kumarobo/PlaRails/Crossover/RailVCoverCV_pointtestasm.png

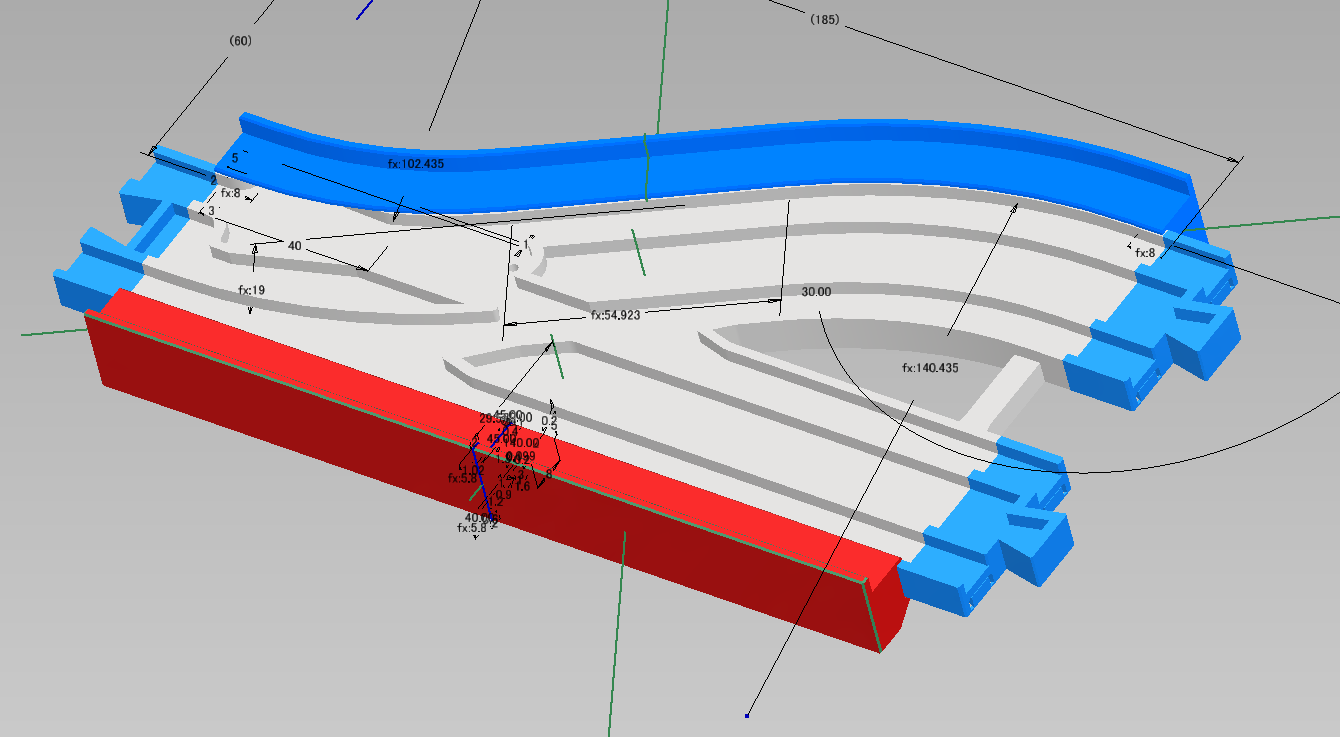
Crossover/RailVCoverCV_pointtestasm.png
