kumarobo/PlaRails/Crossover/RailVCoverCV_S.png

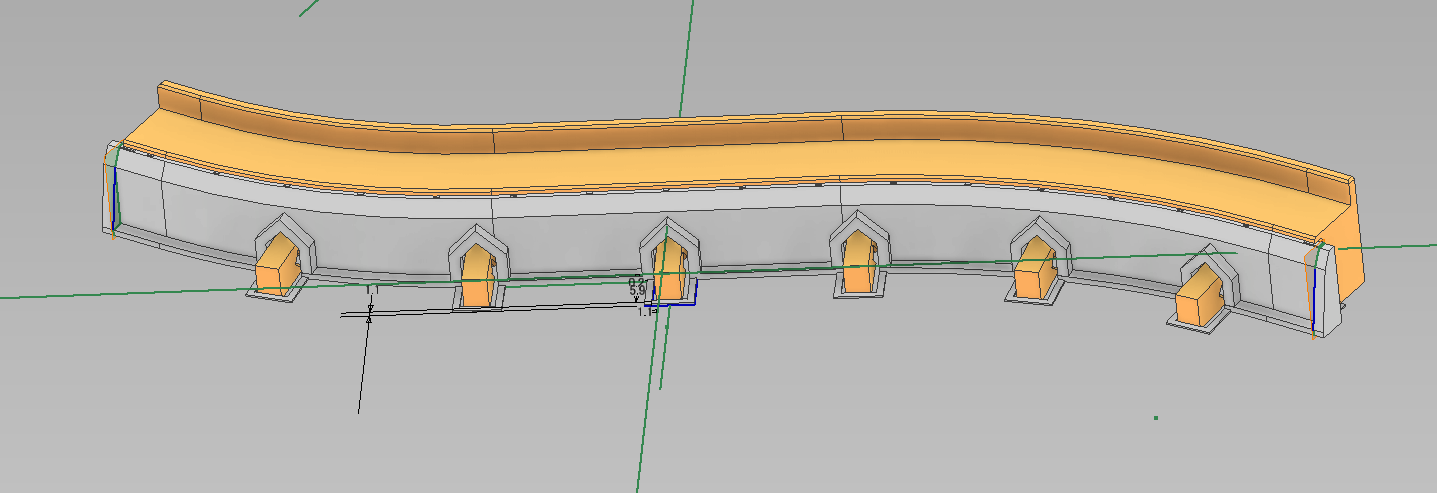
Crossover/RailVCoverCV_S.png
