kumarobo/PlaRails/Crossover/RailVCoverST.png

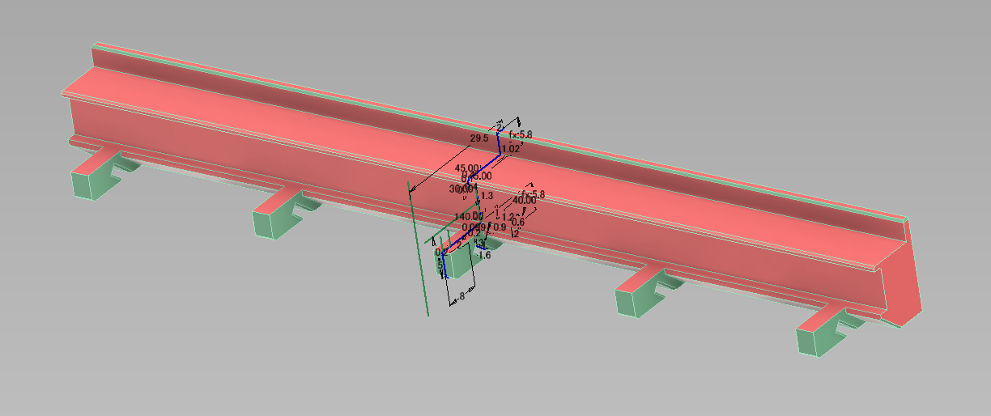
Crossover/RailVCoverST.png
