kumarobo/PlaRails/Crossover/SingleCross.png

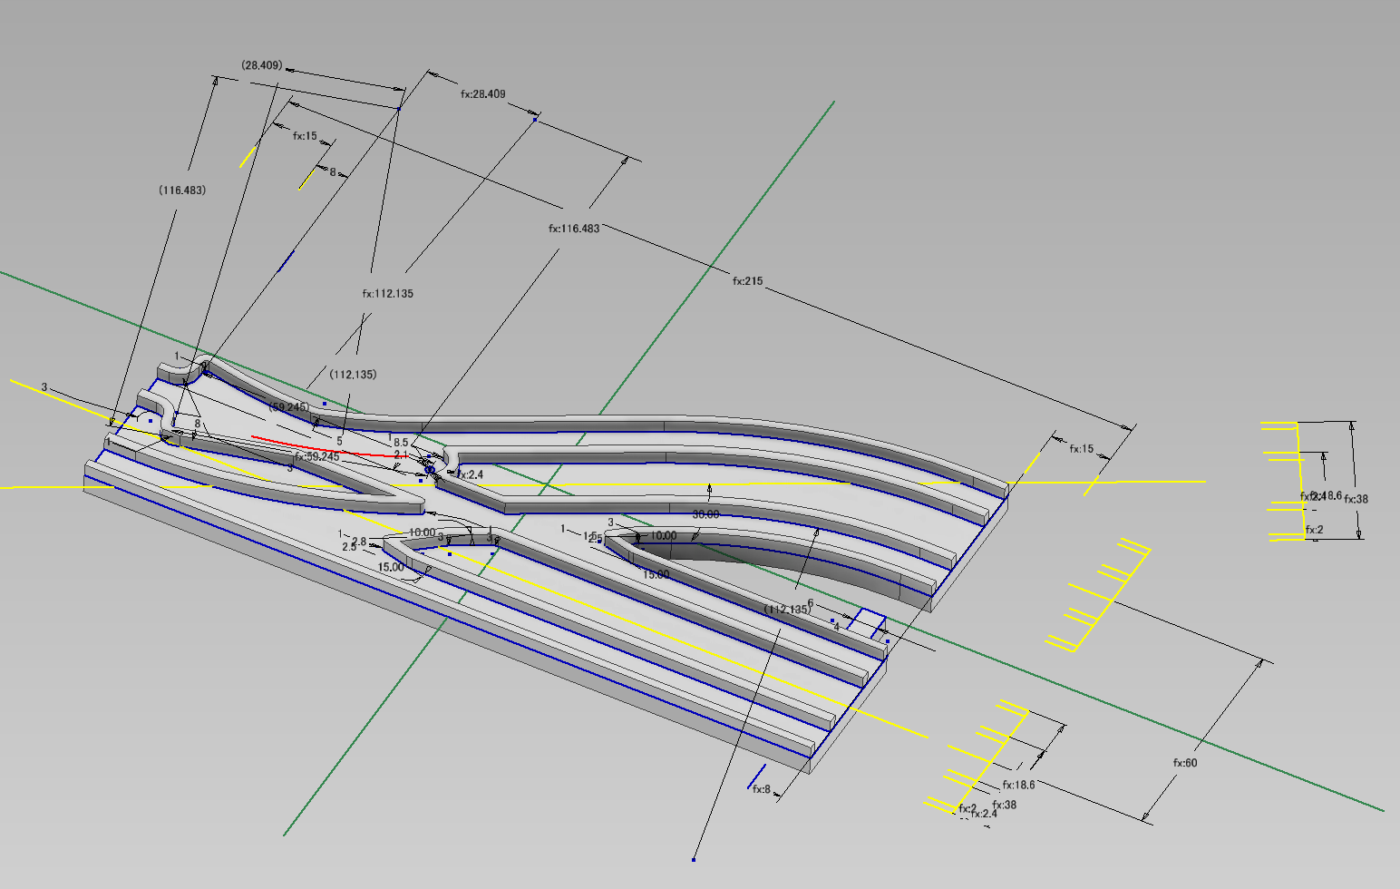
Crossover/SingleCross.png
