kumarobo/PlaRails/Crossover/SingleCrossoverIA.png

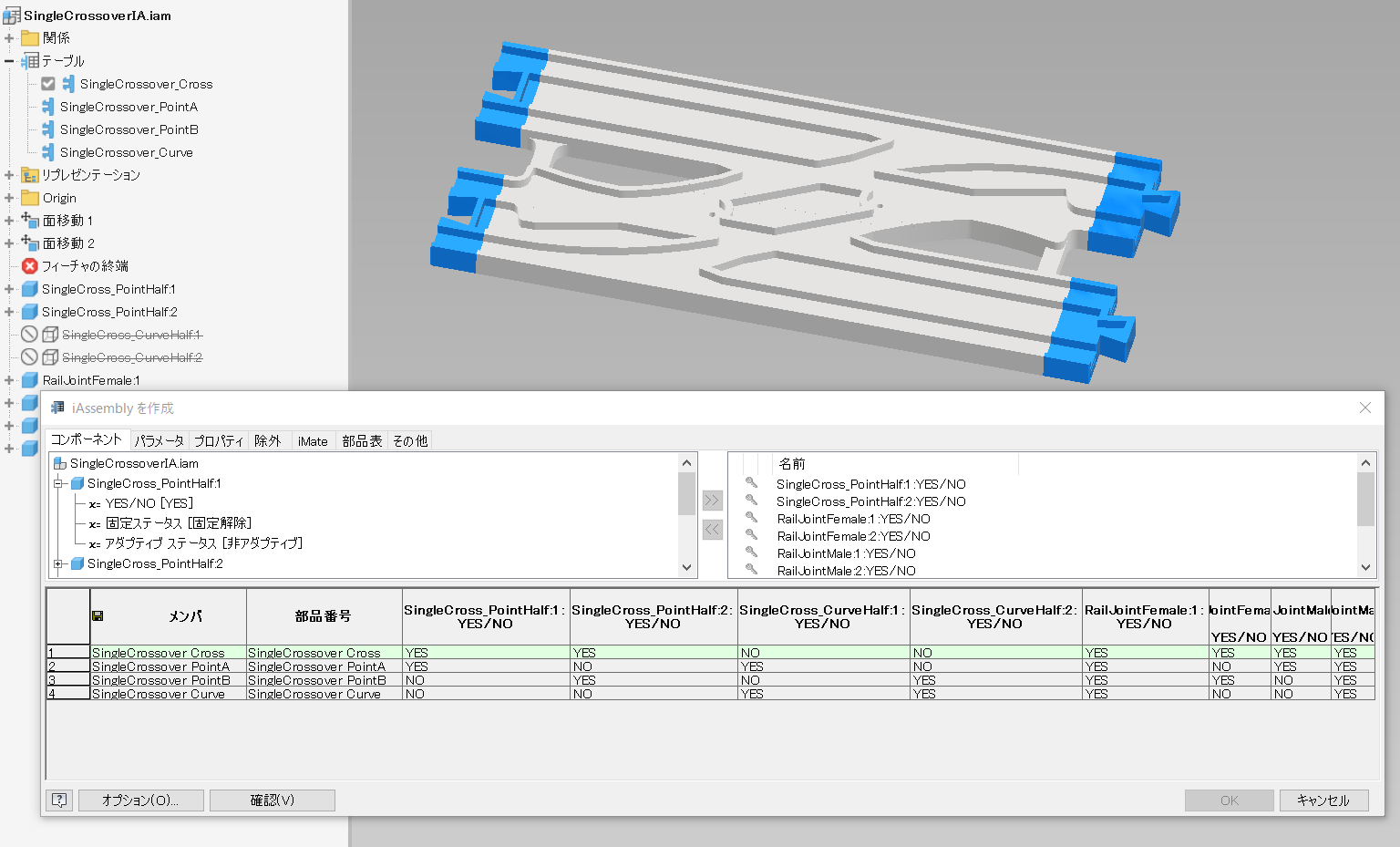
Crossover/SingleCrossoverIA.png
