kumarobo/PlaRails/Crossover/SingleCrossoverIA_Cross.png

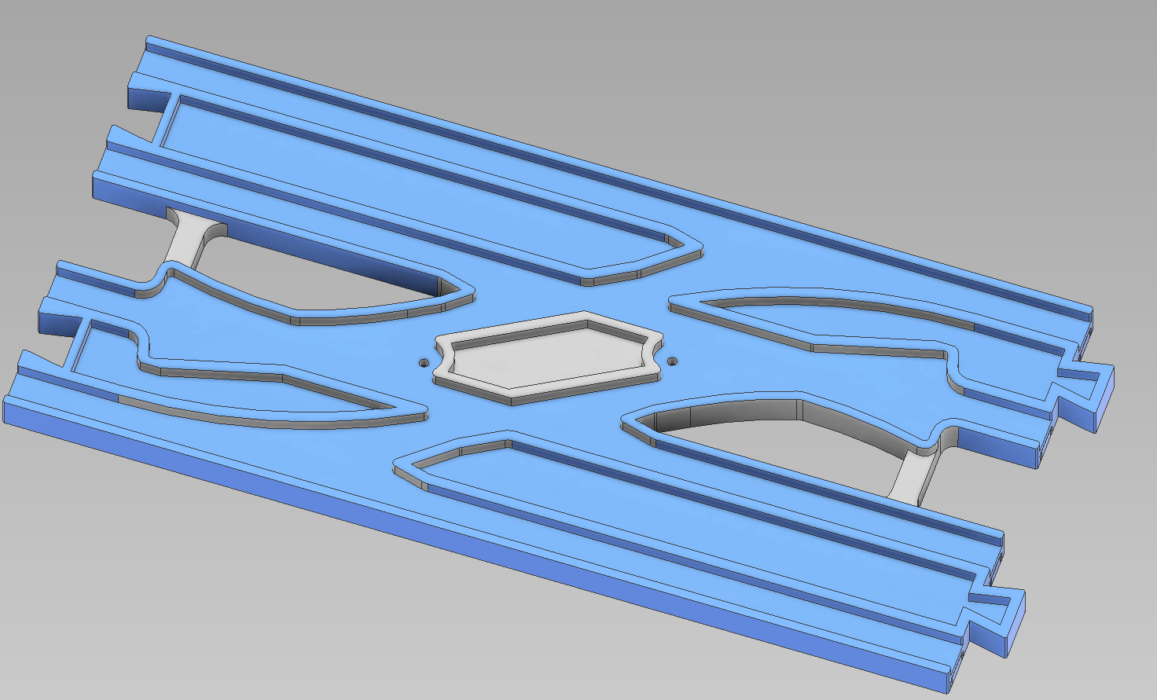
Crossover/SingleCrossoverIA_Cross.png
