kumarobo/PlaRails/Crossover/SingleCrossoverIA_Cross_MIR.png

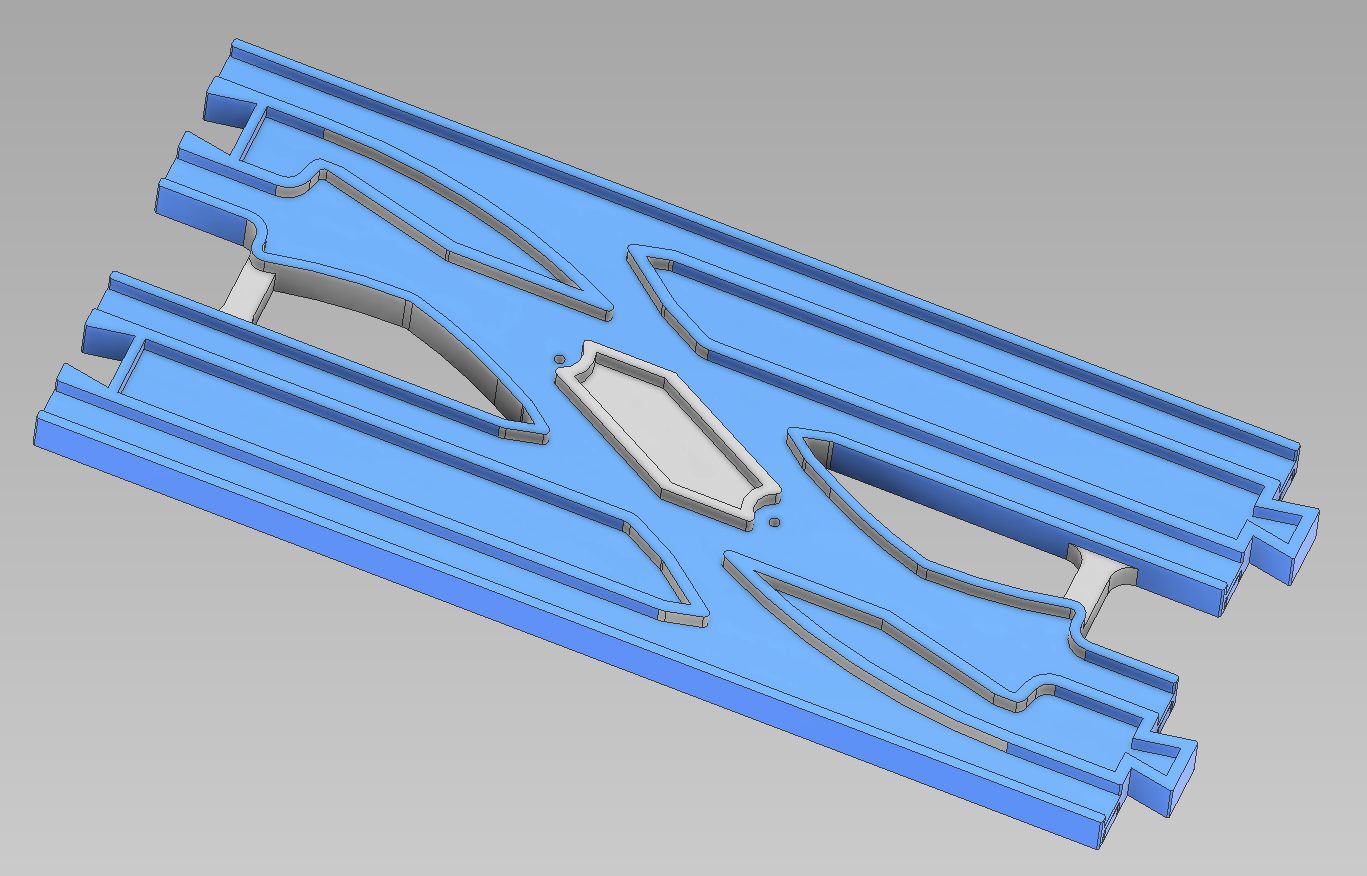
Crossover/SingleCrossoverIA_Cross_MIR.png
