kumarobo/PlaRails/Crossover/SingleCrossoverIA_Curve.png

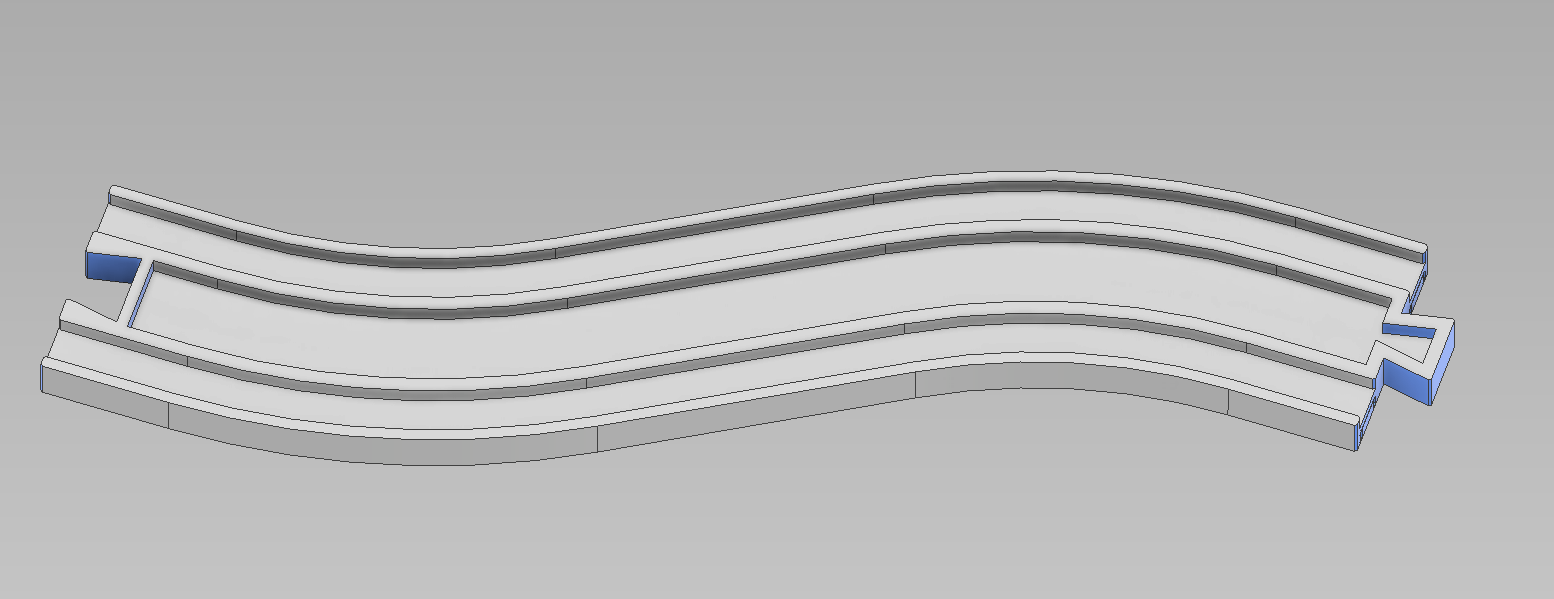
Crossover/SingleCrossoverIA_Curve.png
