kumarobo/PlaRails/Crossover/SingleCrossoverIA_Curve_MIR.png

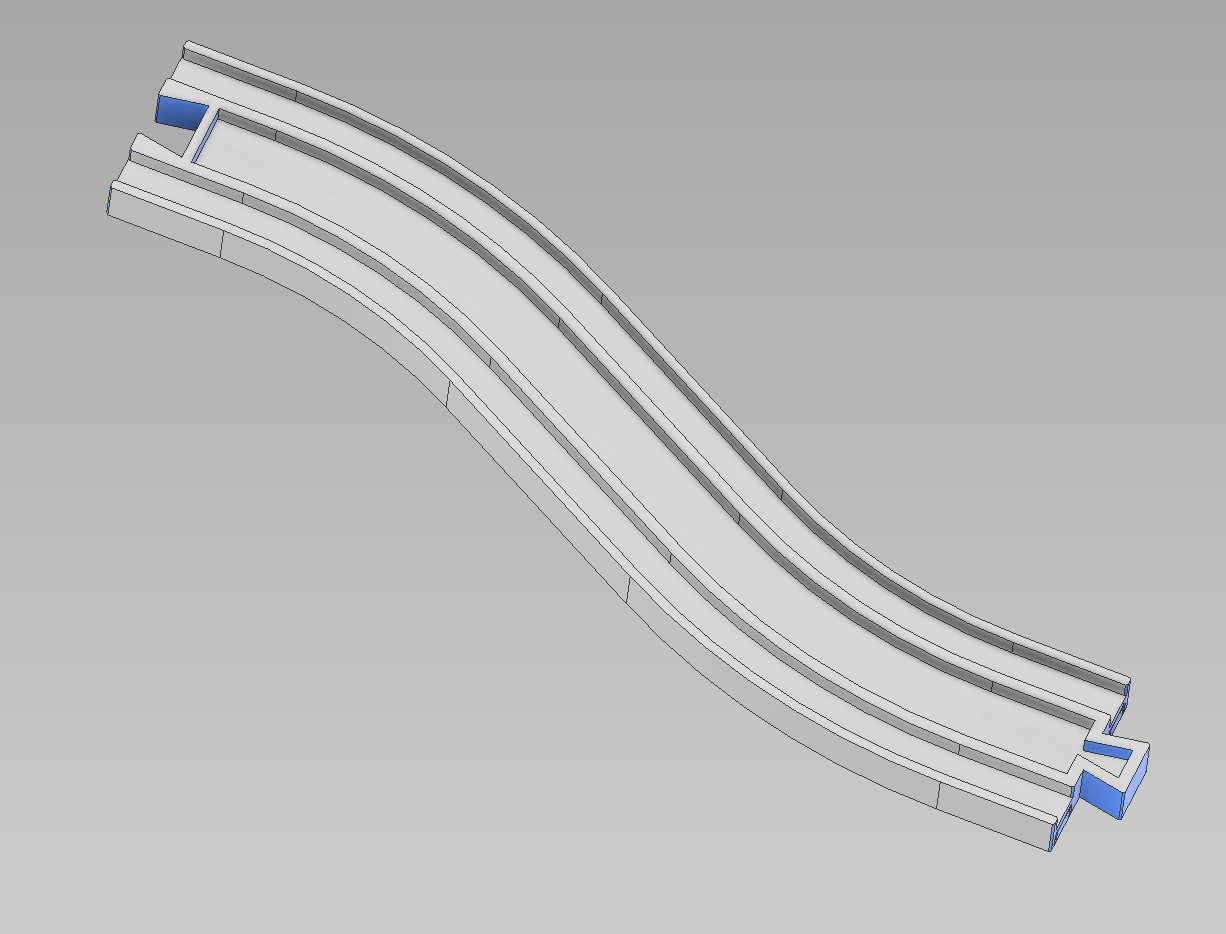
Crossover/SingleCrossoverIA_Curve_MIR.png
