kumarobo/PlaRails/Crossover/SingleCrossoverIA_PointA.png

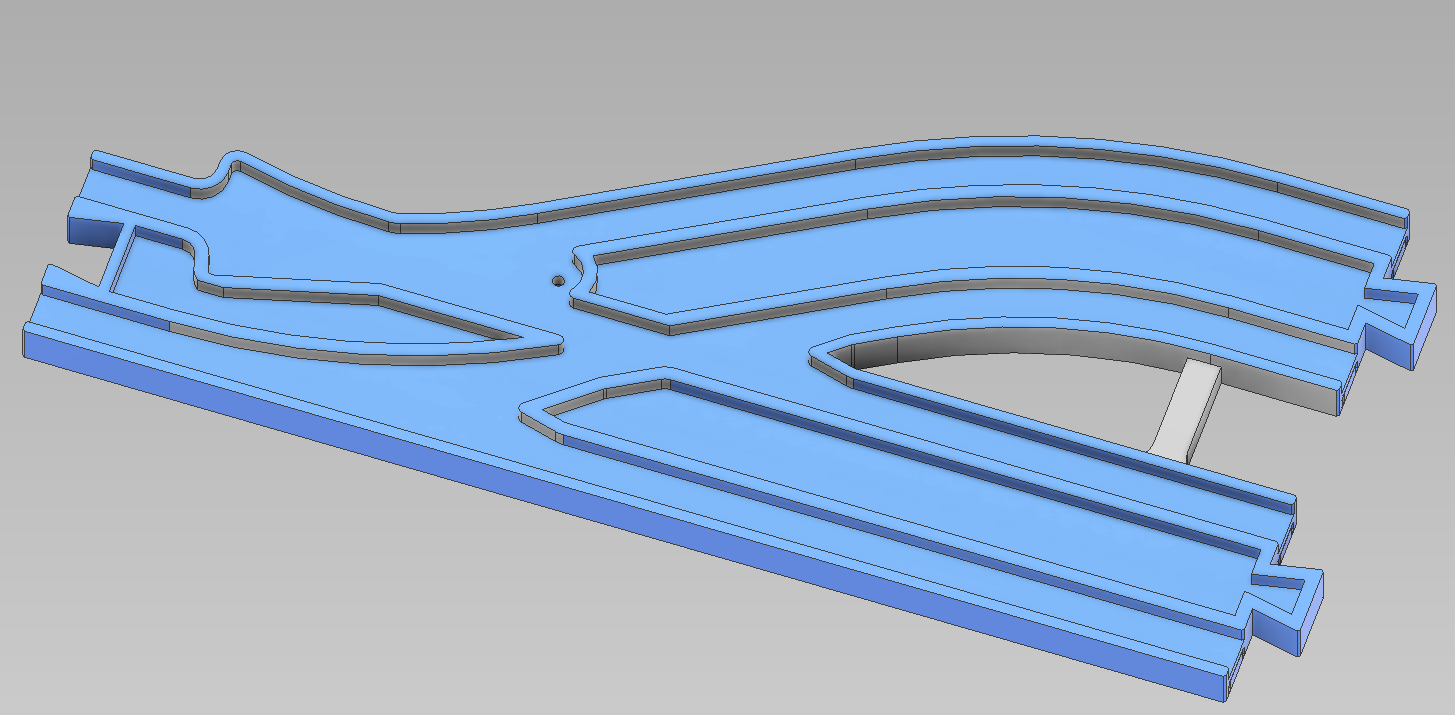
Crossover/SingleCrossoverIA_PointA.png
