kumarobo/PlaRails/Crossover/SingleCrossoverIA_PointA_MIR.png

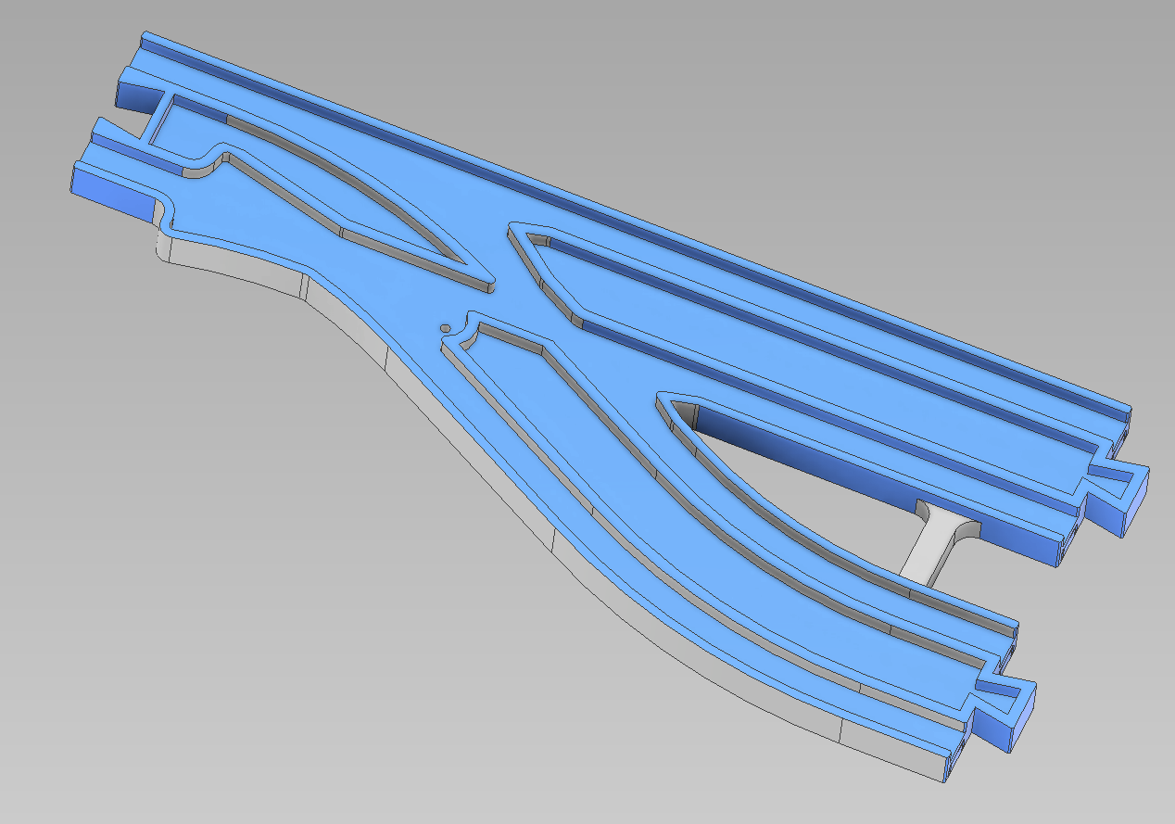
Crossover/SingleCrossoverIA_PointA_MIR.png
