kumarobo/PlaRails/CurveRail/CurveRail-89-25.png

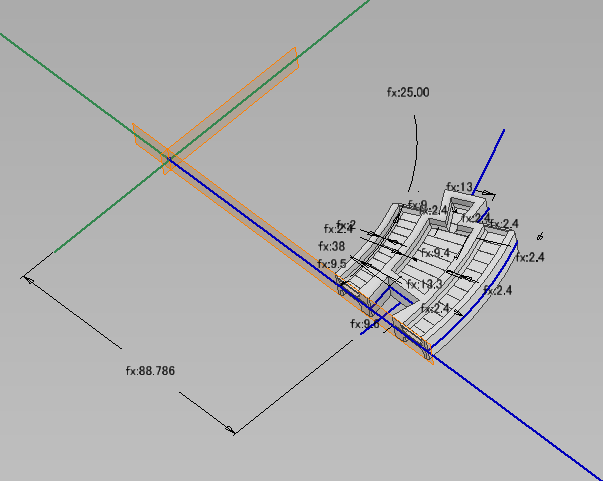
CurveRail/CurveRail-89-25.png
