kumarobo/PlaRails/CurveRail/CurveRail-215-45.png

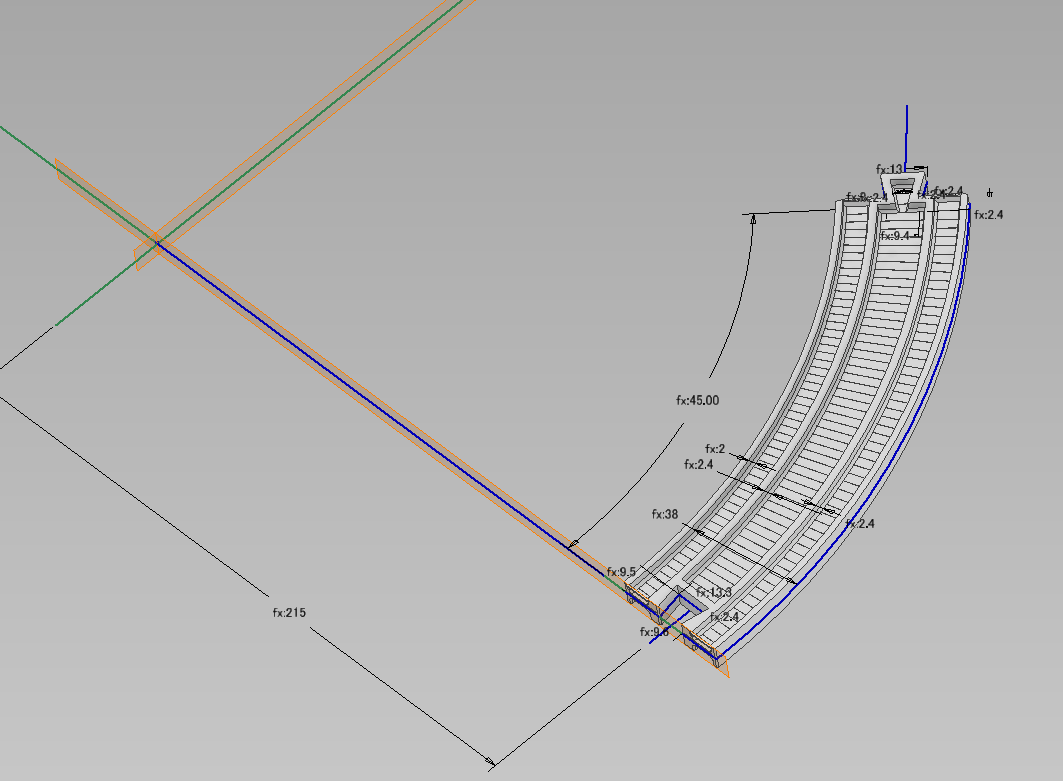
CurveRail/CurveRail-215-45.png
