kumarobo/PlaRails/CurveRail/CurveRail-215half-45.png

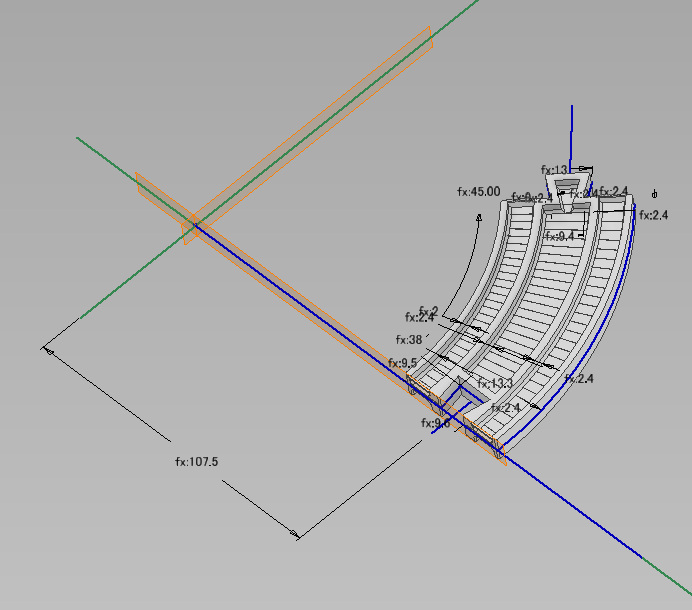
CurveRail/CurveRail-215half-45.png
