kumarobo/PlaRails/CurveRail/CurveRail-215half-90.png

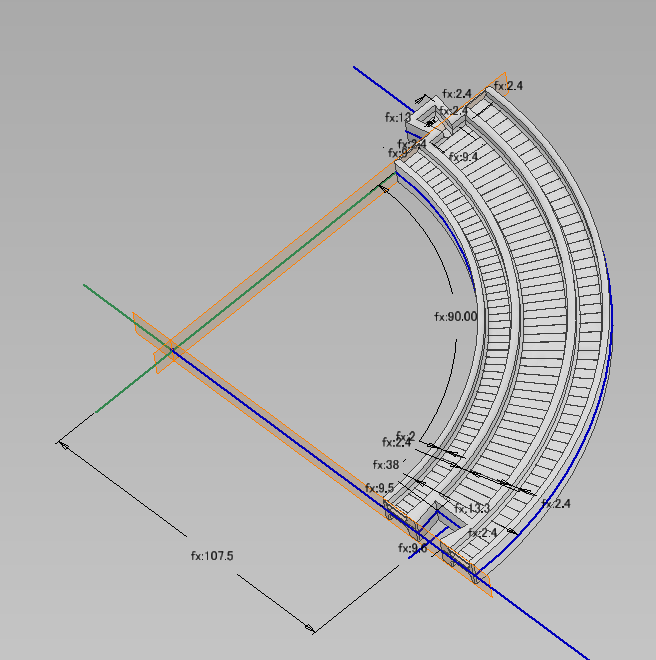
CurveRail/CurveRail-215half-90.png
