kumarobo/PlaRails/CurveRail/CurveRail-342-25.png

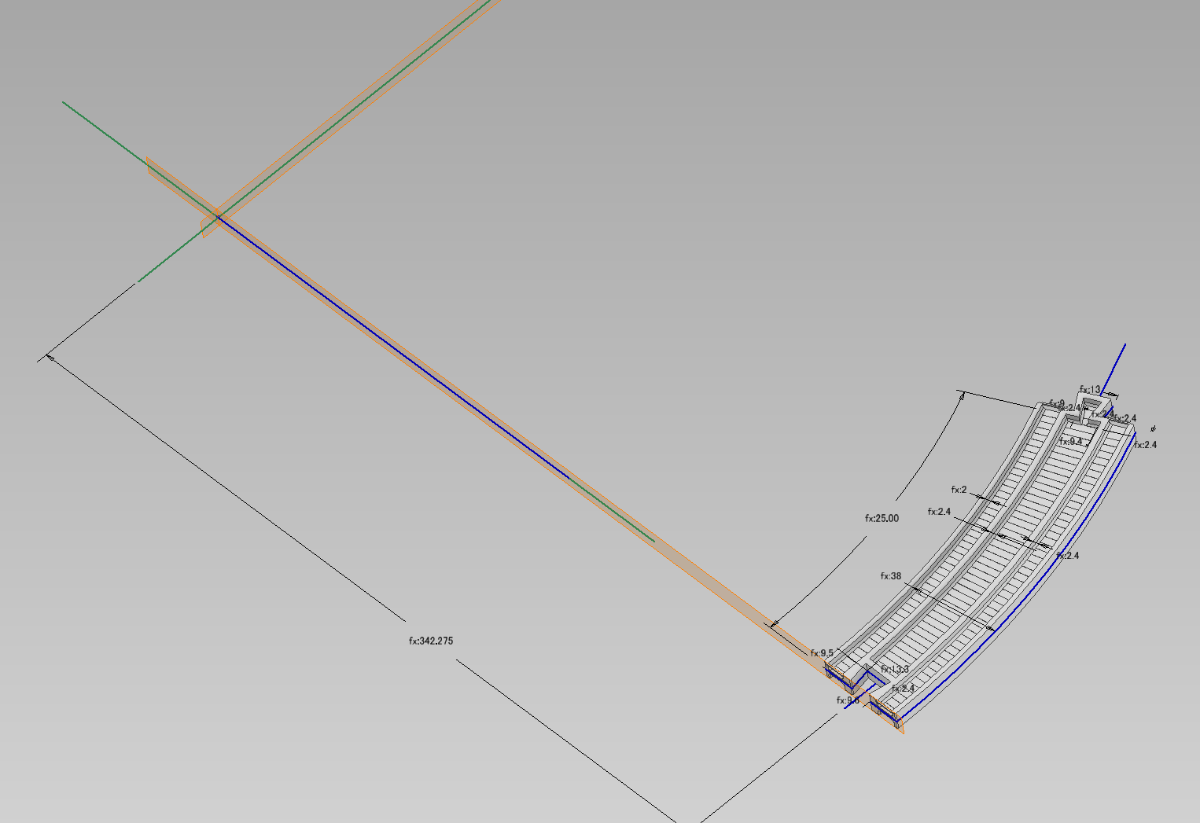
CurveRail/CurveRail-342-25.png
