kumarobo/PlaRails/DoubleCross/DoubleCross.png

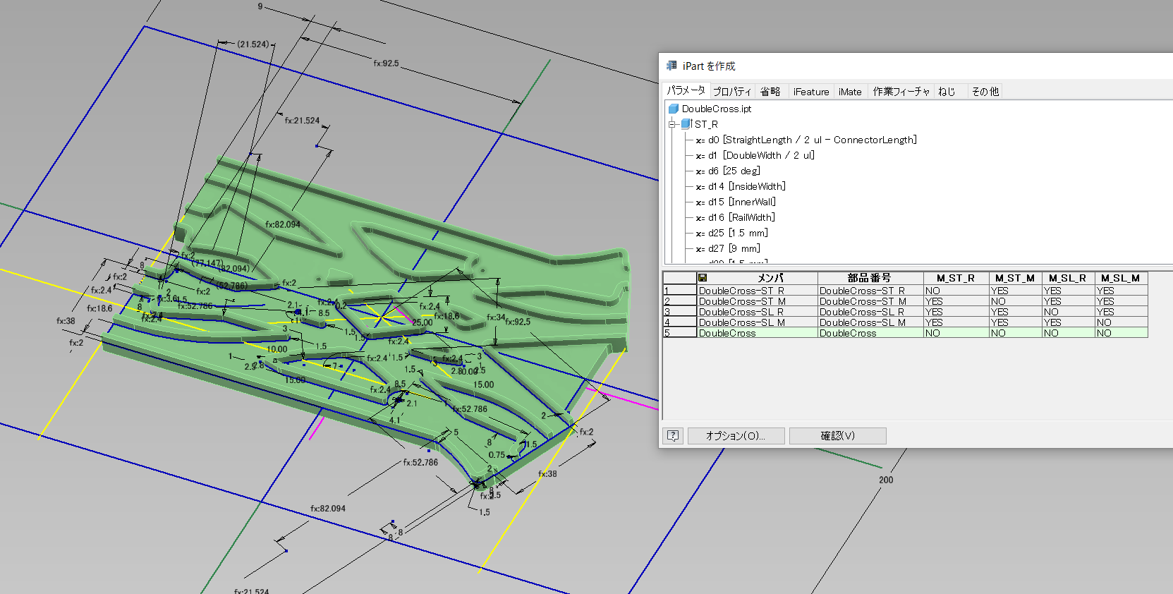
DoubleCross/DoubleCross.png
