kumarobo/PlaRails/DoubleCross/DoubleCross_DoubleSlant.png

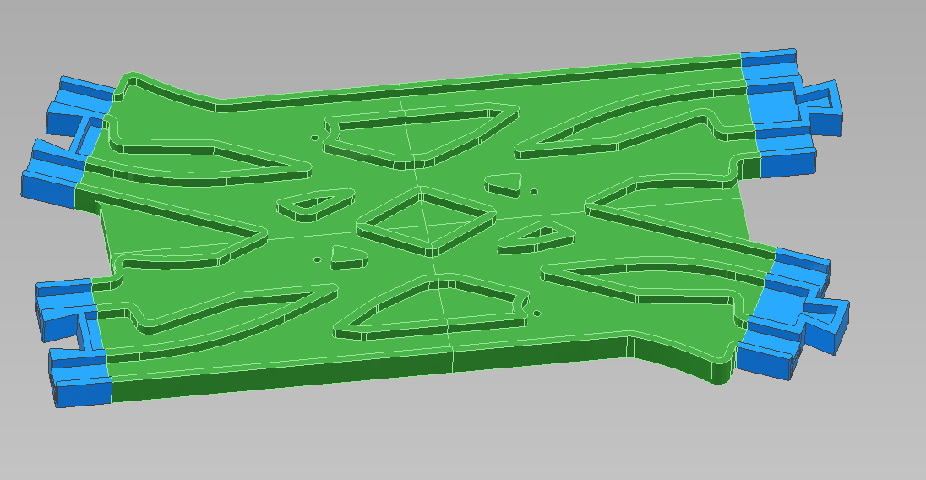
DoubleCross/DoubleCross_DoubleSlant.png
