kumarobo/PlaRails/DoubleCross/DoubleCross_DoubleSlip_C.png

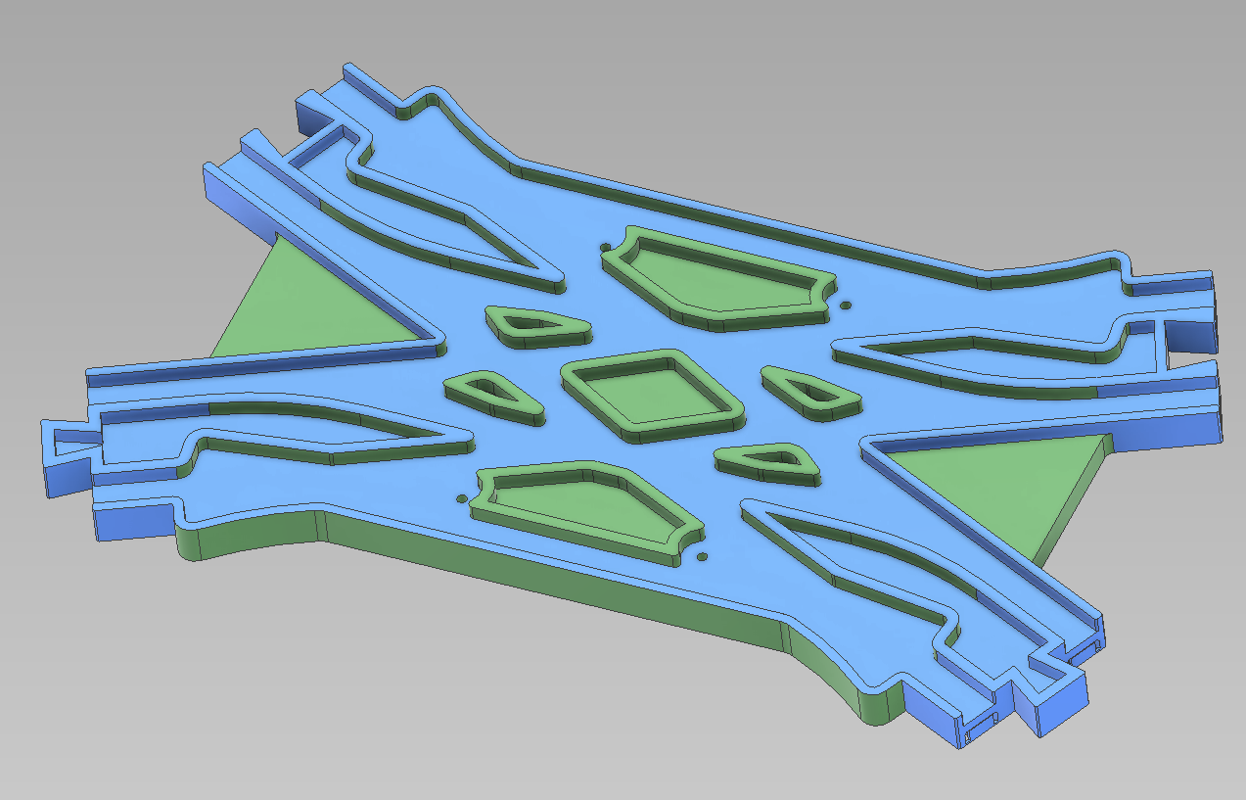
DoubleCross/DoubleCross_DoubleSlip_C.png
