kumarobo/PlaRails/DoubleCross/DoubleCross_Rturn_C.png

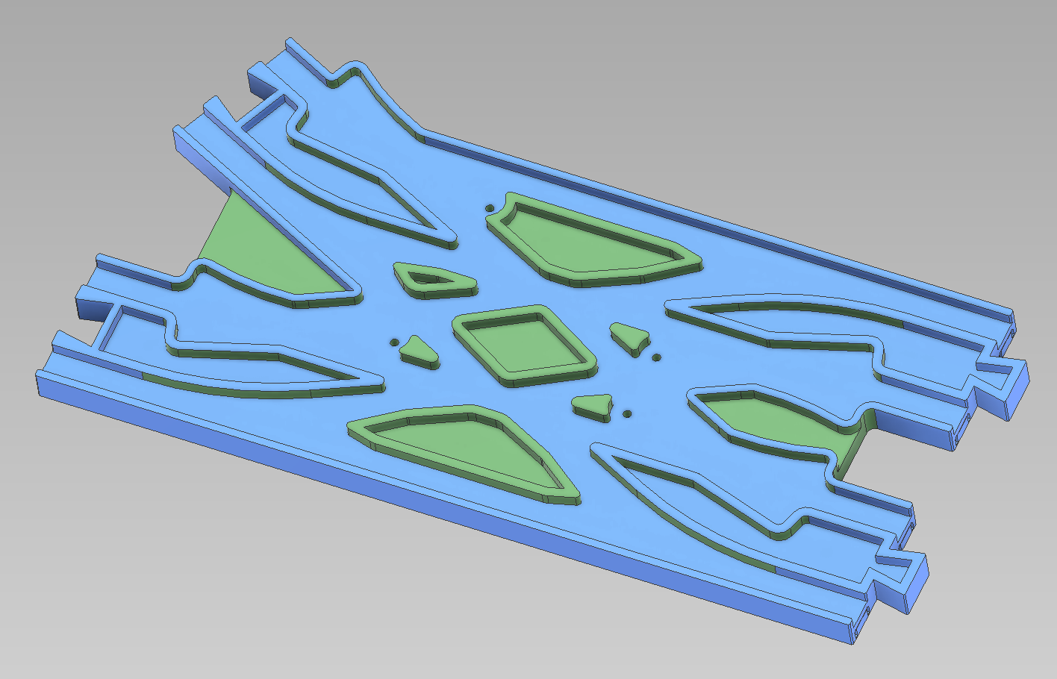
DoubleCross/DoubleCross_Rturn_C.png
