kumarobo/PlaRails/DoubleCross/DoubleCross_Straight_C.png

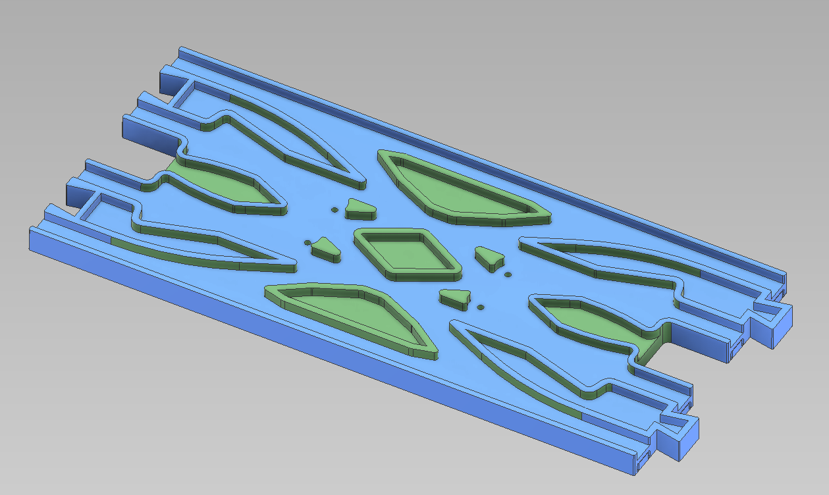
DoubleCross/DoubleCross_Straight_C.png
