kumarobo/PlaRails/DoubleCross/DoubleCross_SymWiden_C.png

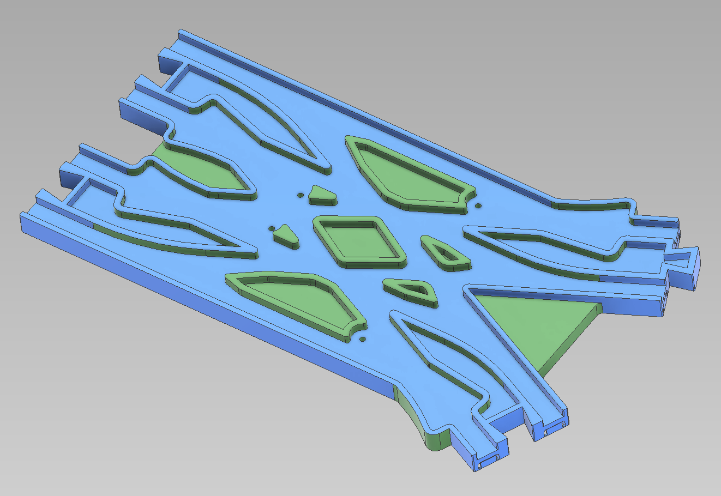
DoubleCross/DoubleCross_SymWiden_C.png
