kumarobo/PlaRails/DoubleSlip/CrossRail_C_DSS.png

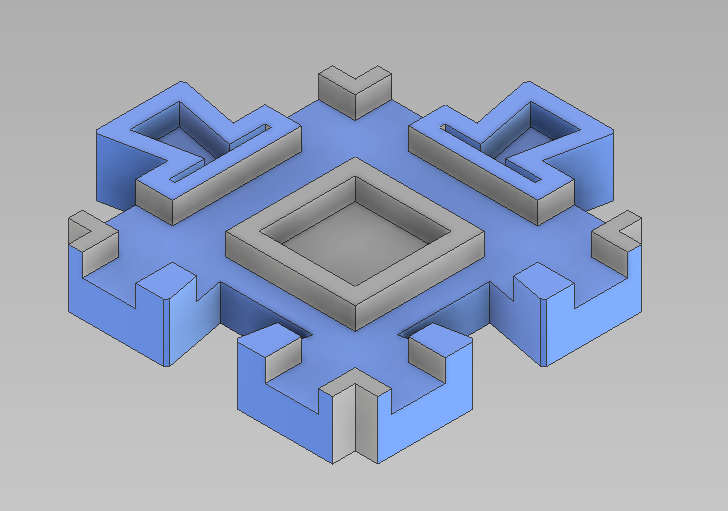
DoubleSlip/CrossRail_C_DSS.png
