kumarobo/PlaRails/DoubleSlip/DoubleSlipHR_asmtest.png

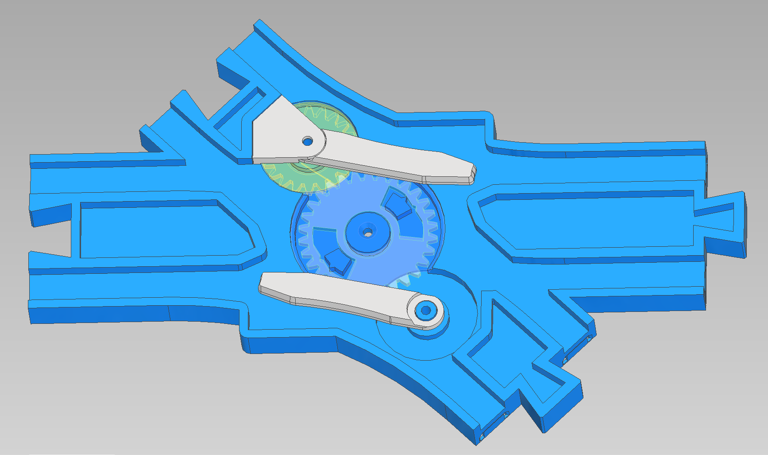
DoubleSlip/DoubleSlipHR_asmtest.png
