kumarobo/PlaRails/DoubleSlip/DoubleSlipHR_C_H_H.png

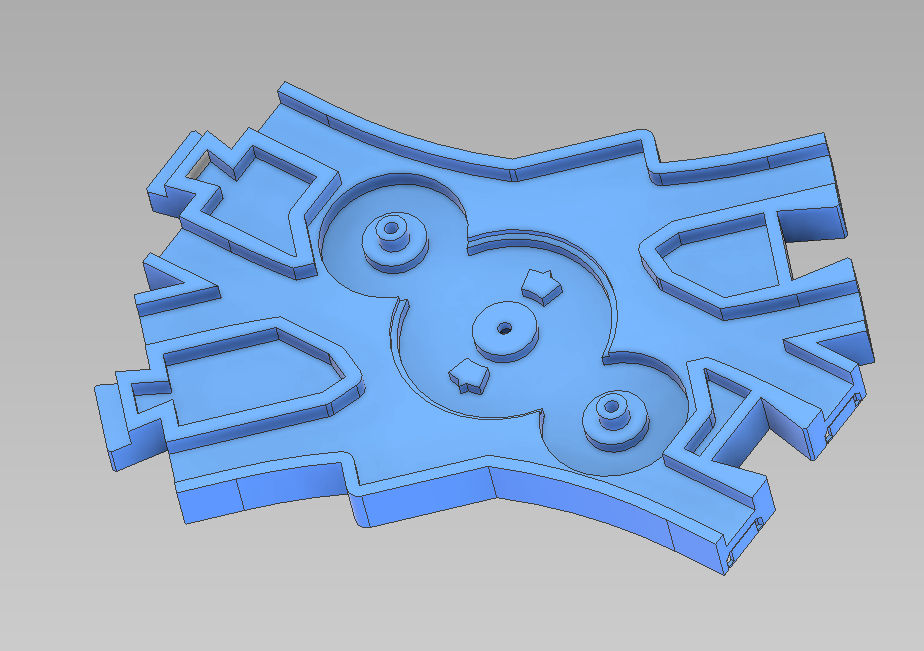
DoubleSlip/DoubleSlipHR_C_H_H.png
