kumarobo/PlaRails/DoubleSlip/DoubleSlipHR_C_H_HS.png

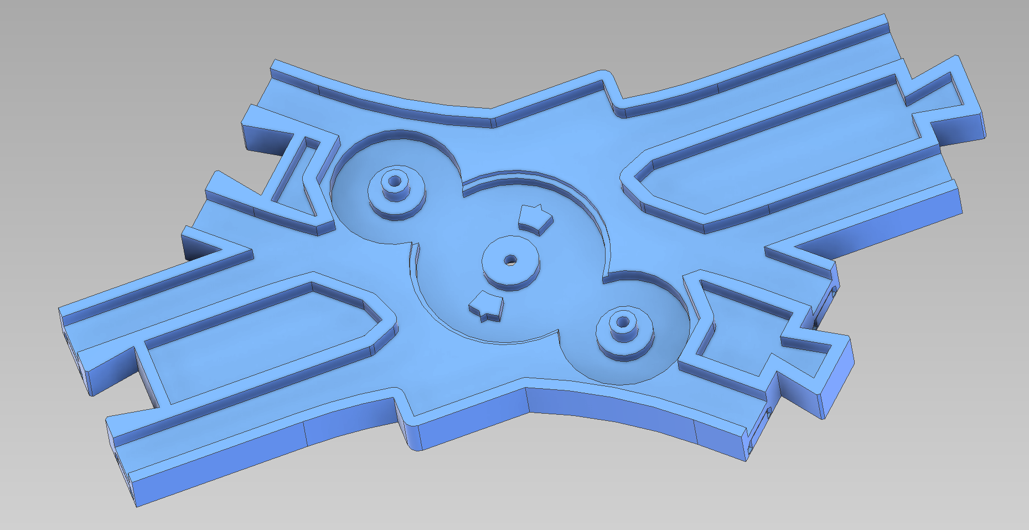
DoubleSlip/DoubleSlipHR_C_H_HS.png
