kumarobo/PlaRails/DoubleSlip/DoubleSlipHR_C_HS_H.png

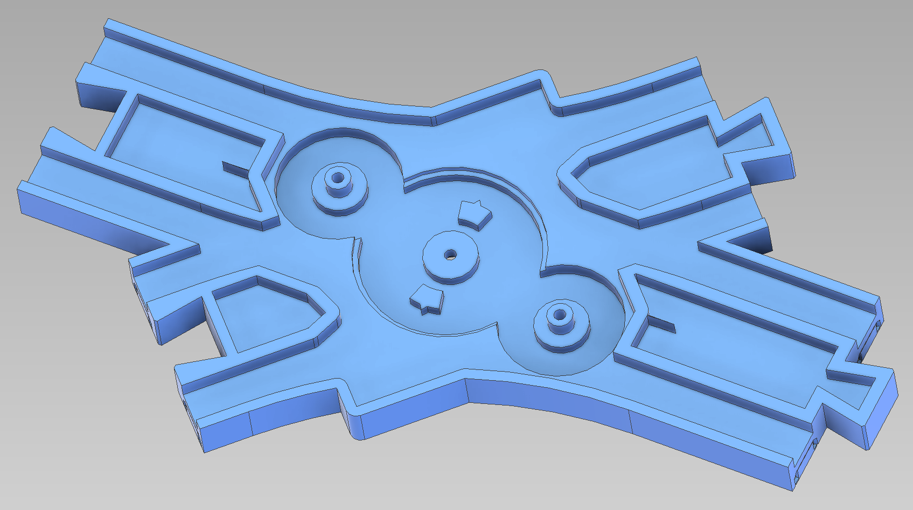
DoubleSlip/DoubleSlipHR_C_HS_H.png
