kumarobo/PlaRails/Misc/AsterMale_6.png

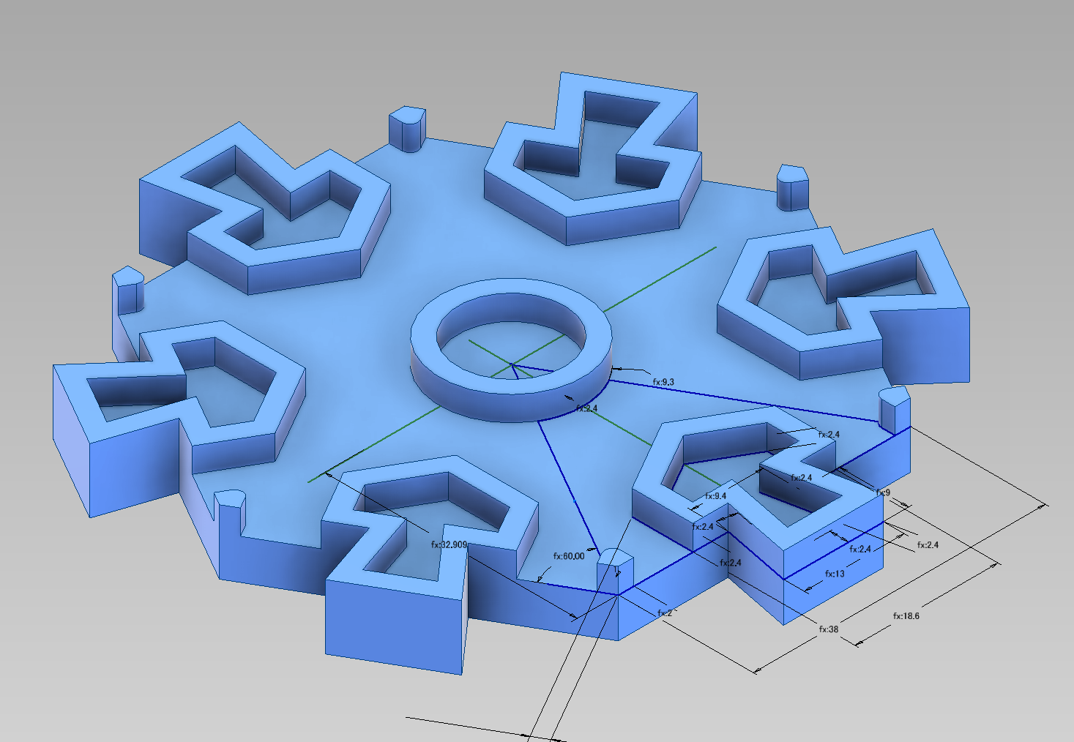
Misc/AsterMale_6.png
