kumarobo/PlaRails/PocketTrackPoint/PocketPoint.png

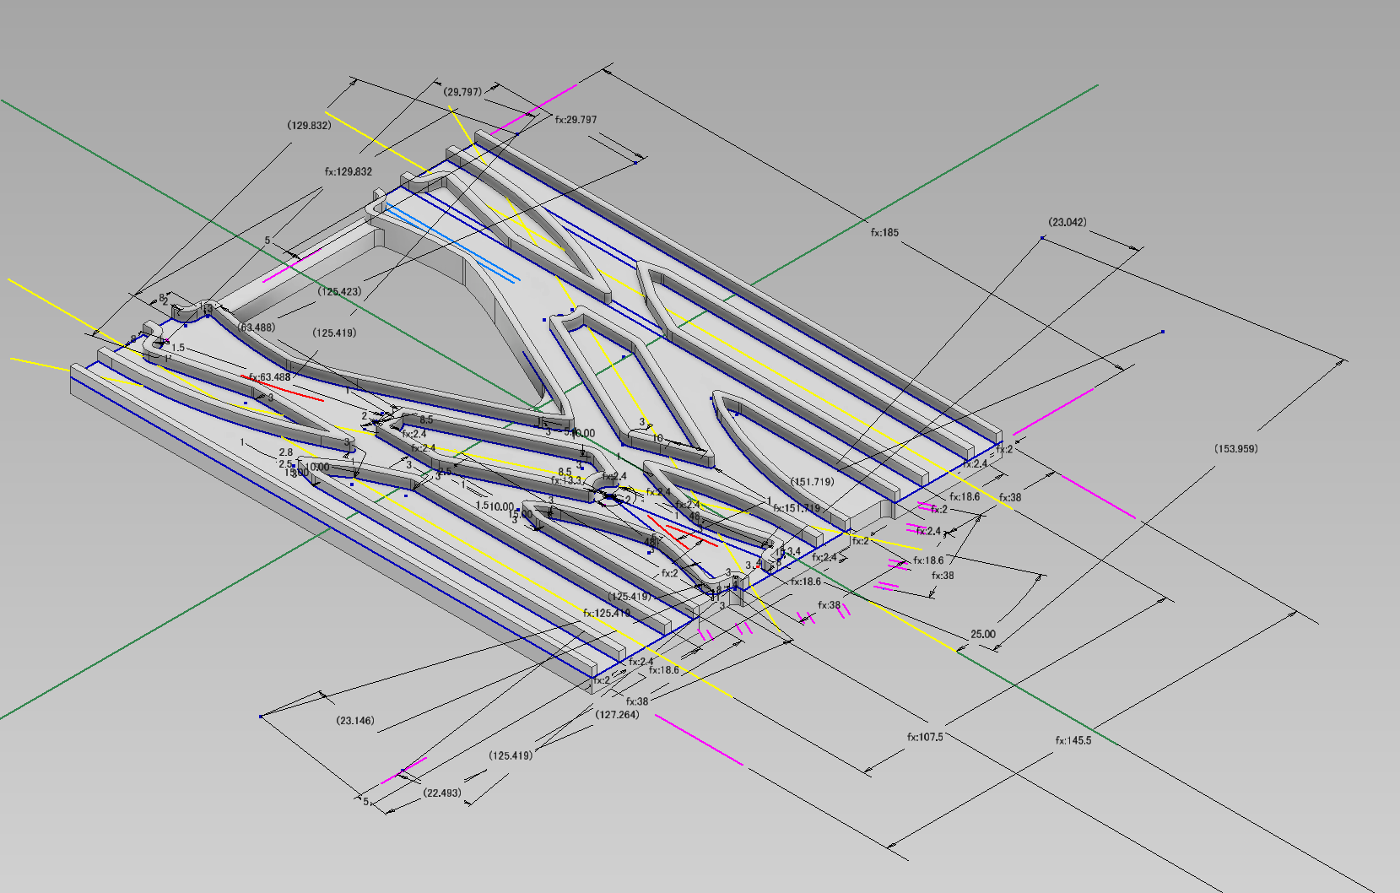
PocketTrackPoint/PocketPoint.png
