kumarobo/PlaRails/PocketTrackPoint/PocketPoint_C.png

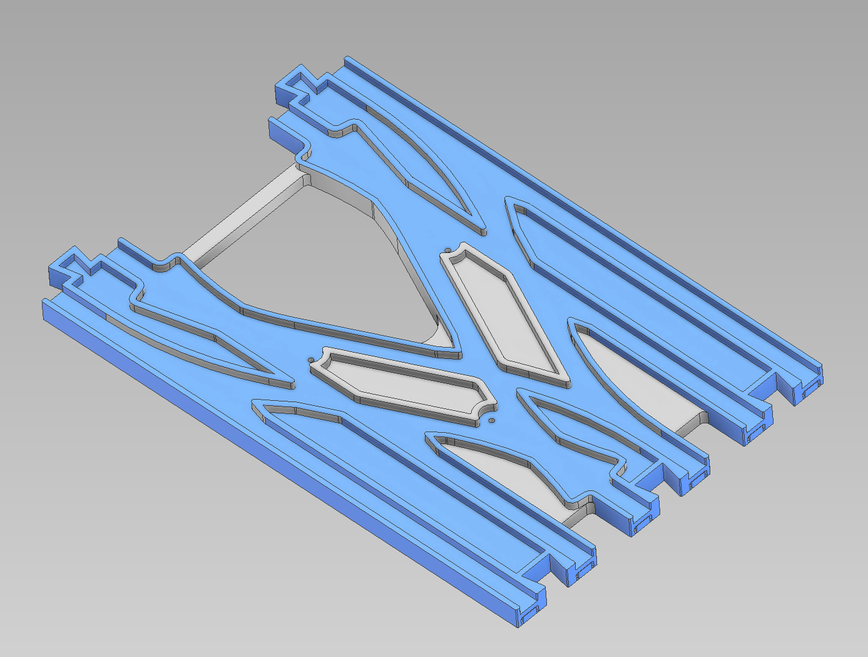
PocketTrackPoint/PocketPoint_C.png
