kumarobo/PlaRails/ShiftRail/ShiftRail_C.png

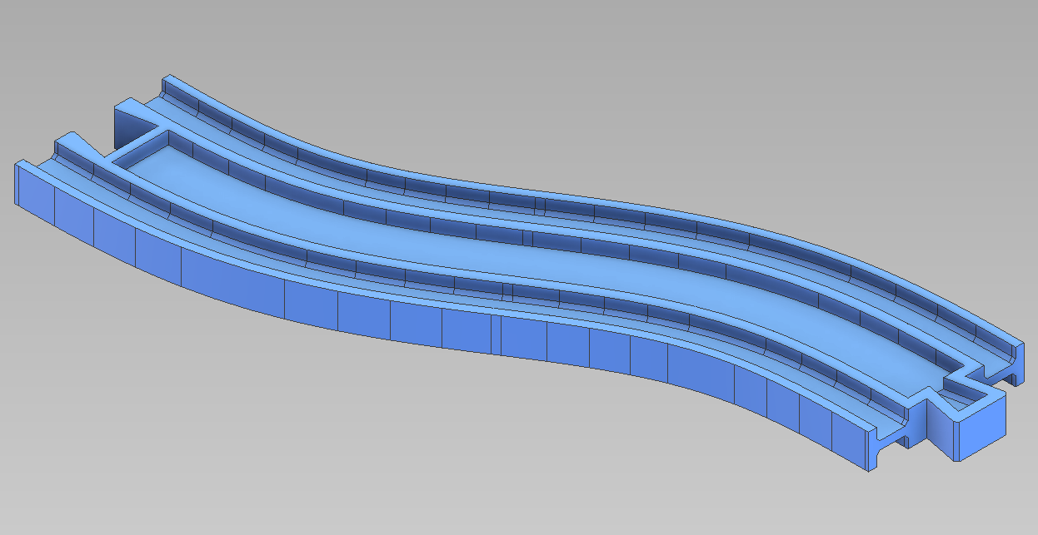
ShiftRail/ShiftRail_C.png
