kumarobo/PlaRails/ShiftRail/ShiftRail_ipt.png

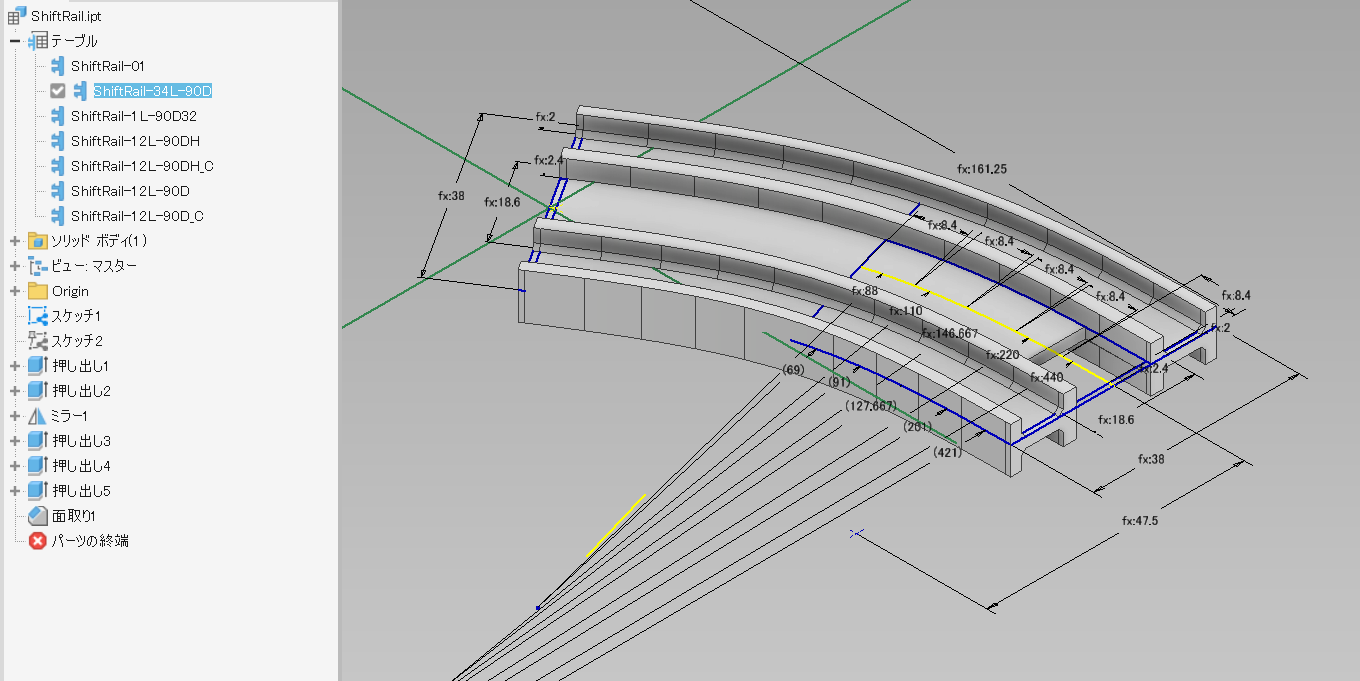
ShiftRail/ShiftRail_ipt.png
