kumarobo/PlaRails/ShiftRail/ShiftRail_S_1L_HDL32.png

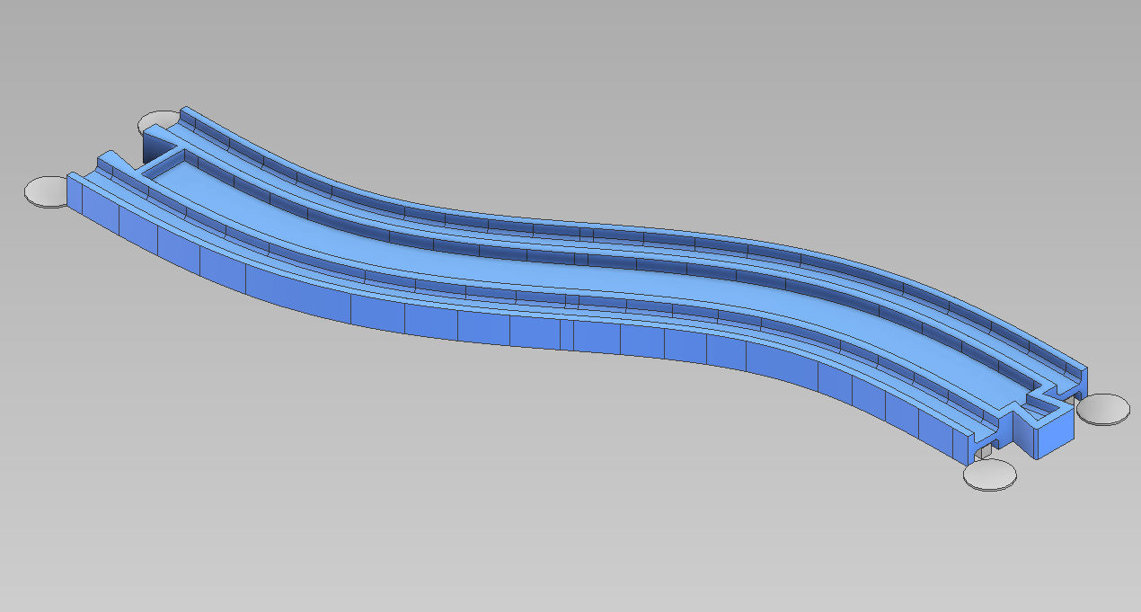
ShiftRail/ShiftRail_S_1L_HDL32.png
