kumarobo/PlaRails/ShiftRail/ShiftRail_S_12L_HLD12.png

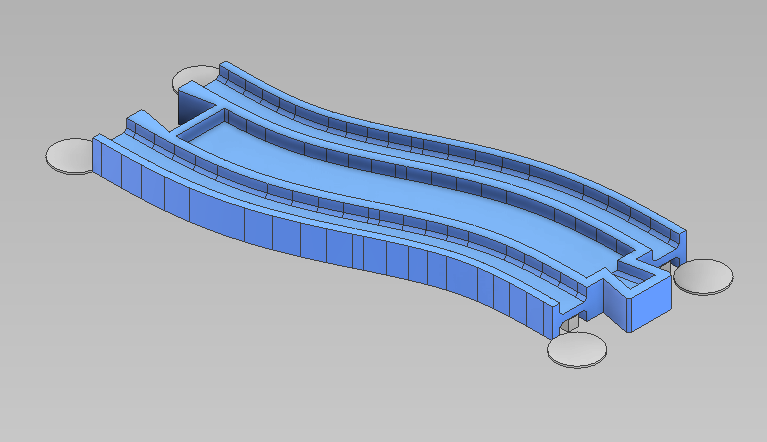
ShiftRail/ShiftRail_S_12L_HLD12.png
