kumarobo/PlaRails/ShiftRail/ShiftRail_S_12L_HLD12_C.png

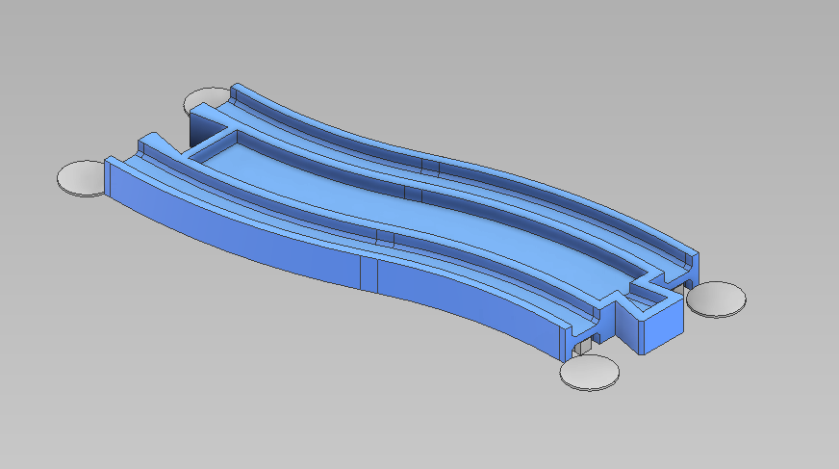
ShiftRail/ShiftRail_S_12L_HLD12_C.png
