kumarobo/PlaRails/ShiftRail/ShiftRail_S_34L_HLD.png

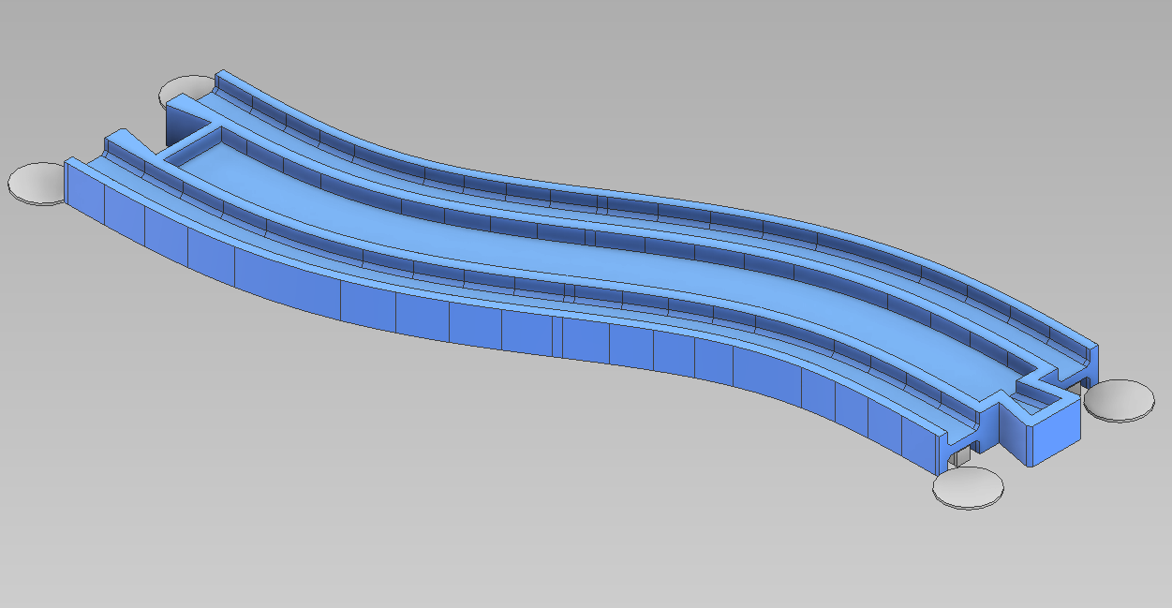
ShiftRail/ShiftRail_S_34L_HLD.png
