kumarobo/PlaRails/SimpleSlope/Slope_HighEnd_C.png

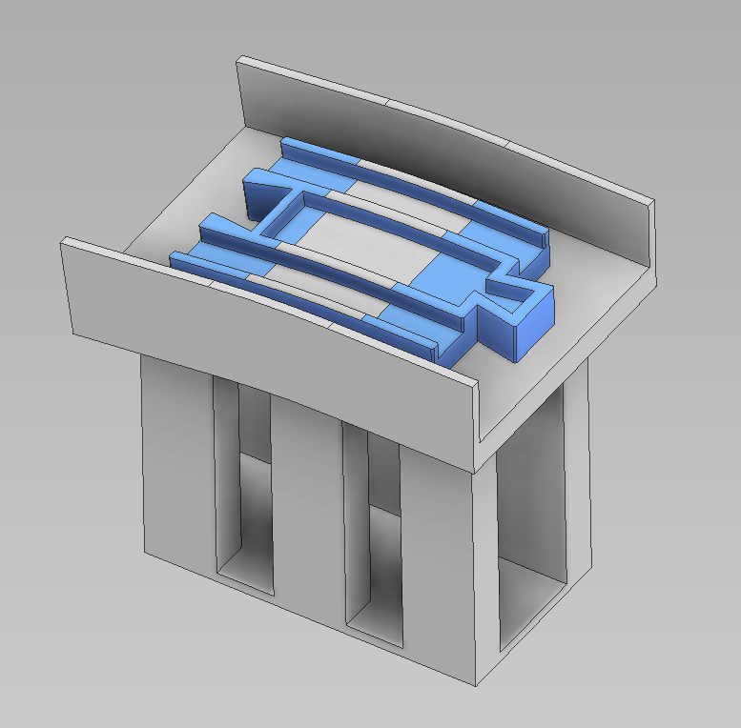
SimpleSlope/Slope_HighEnd_C.png
