kumarobo/PlaRails/SimpleSlope/Slope_LowEnd_C.png

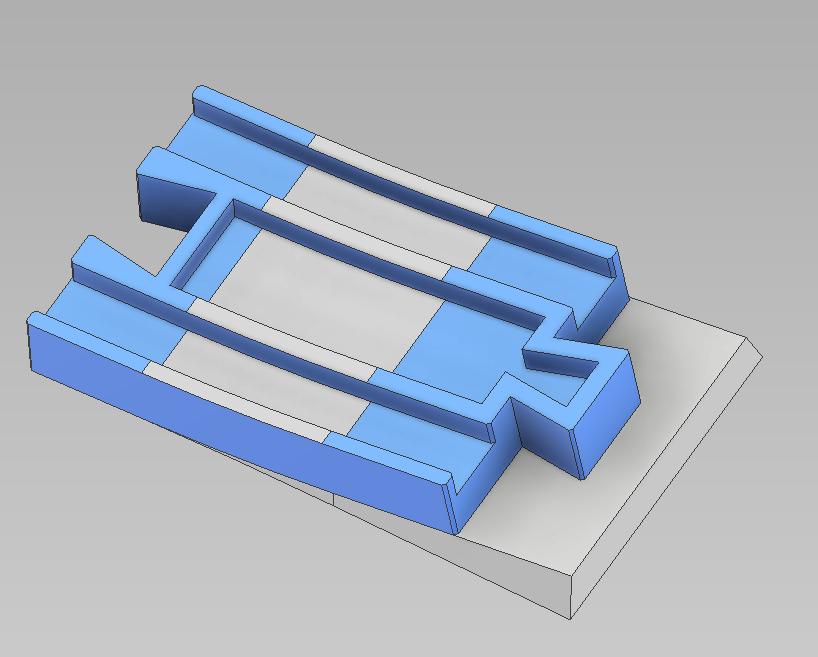
SimpleSlope/Slope_LowEnd_C.png
