kumarobo/PlaRails/StraightRail/StraightRail_C_26FF.png

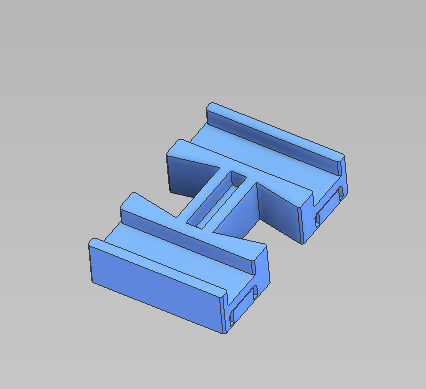
StraightRail/StraightRail_C_26FF.png
