kumarobo/PlaRails/StraightRail/StraightRail_C_26MM.png

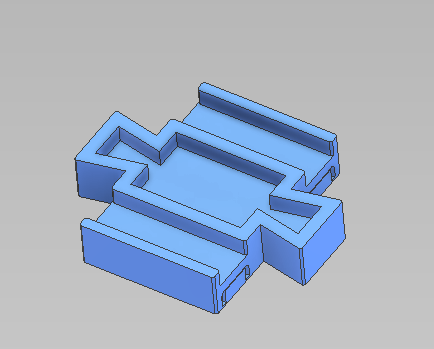
StraightRail/StraightRail_C_26MM.png
