kumarobo/PlaRails/StraightRail/StraightRail_C_60MM.png

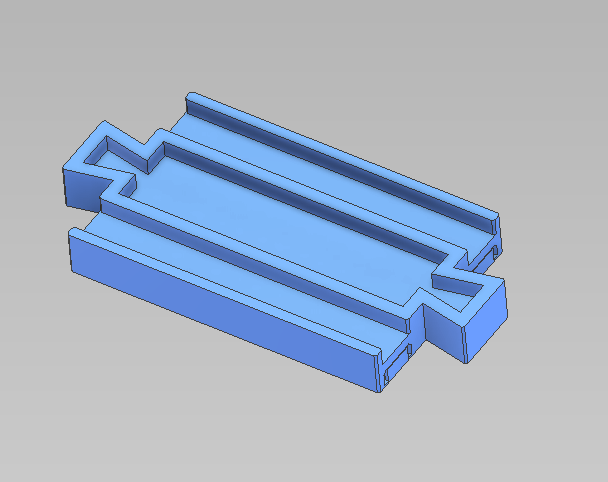
StraightRail/StraightRail_C_60MM.png
