kumarobo/PlaRails/StraightRail/StraightRail_C_DSSMF.png

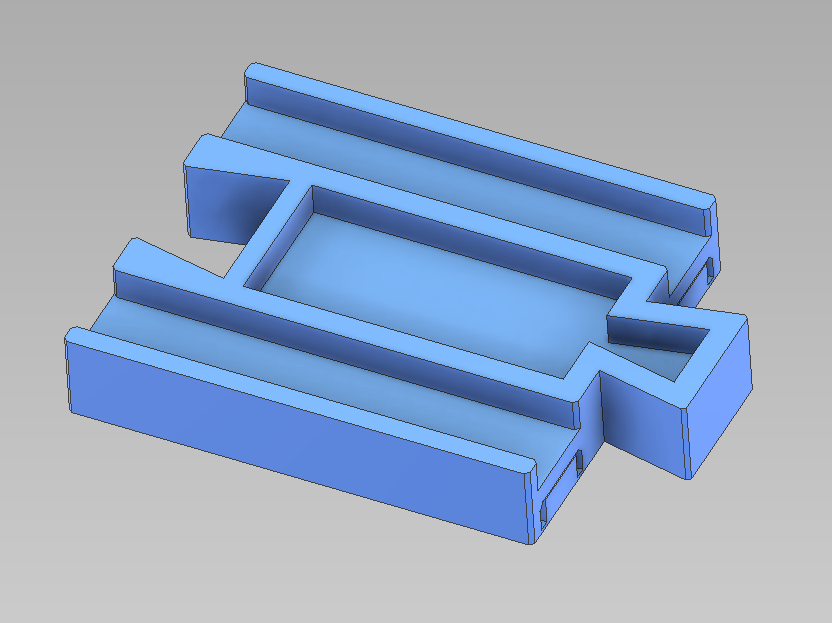
StraightRail/StraightRail_C_DSSMF.png
