kumarobo/PlaRails/TrussCC/TrussCC_box.png

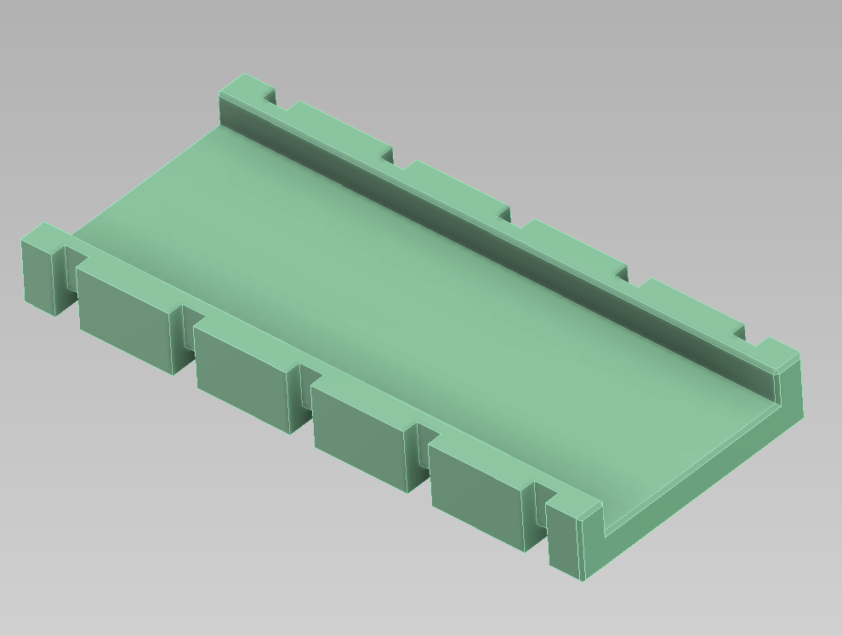
TrussCC/TrussCC_box.png
