kumarobo/PlaRails/ViaductPillar/StandardPillarCover.png

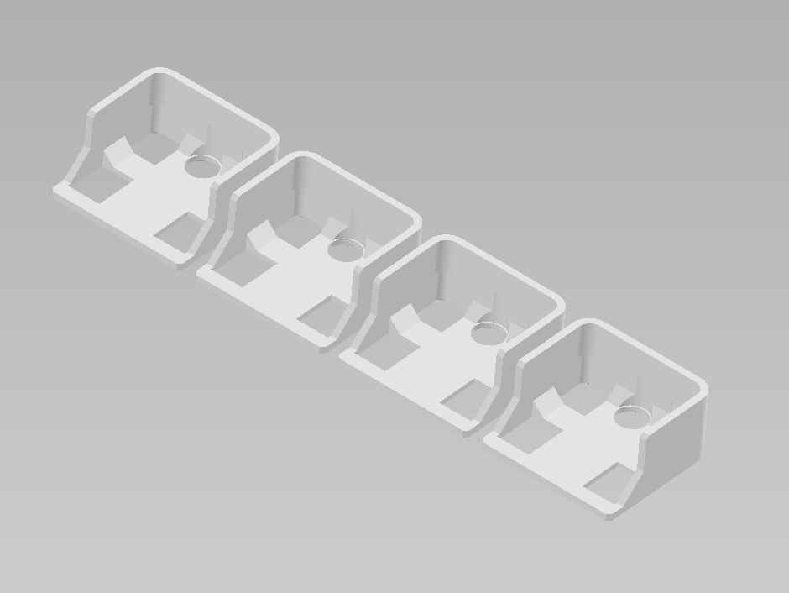
ViaductPillar/StandardPillarCover.png
