kumarobo/PlaRails/ViaductPillarUnit/Viaduct_HorizontalSingle_C.png

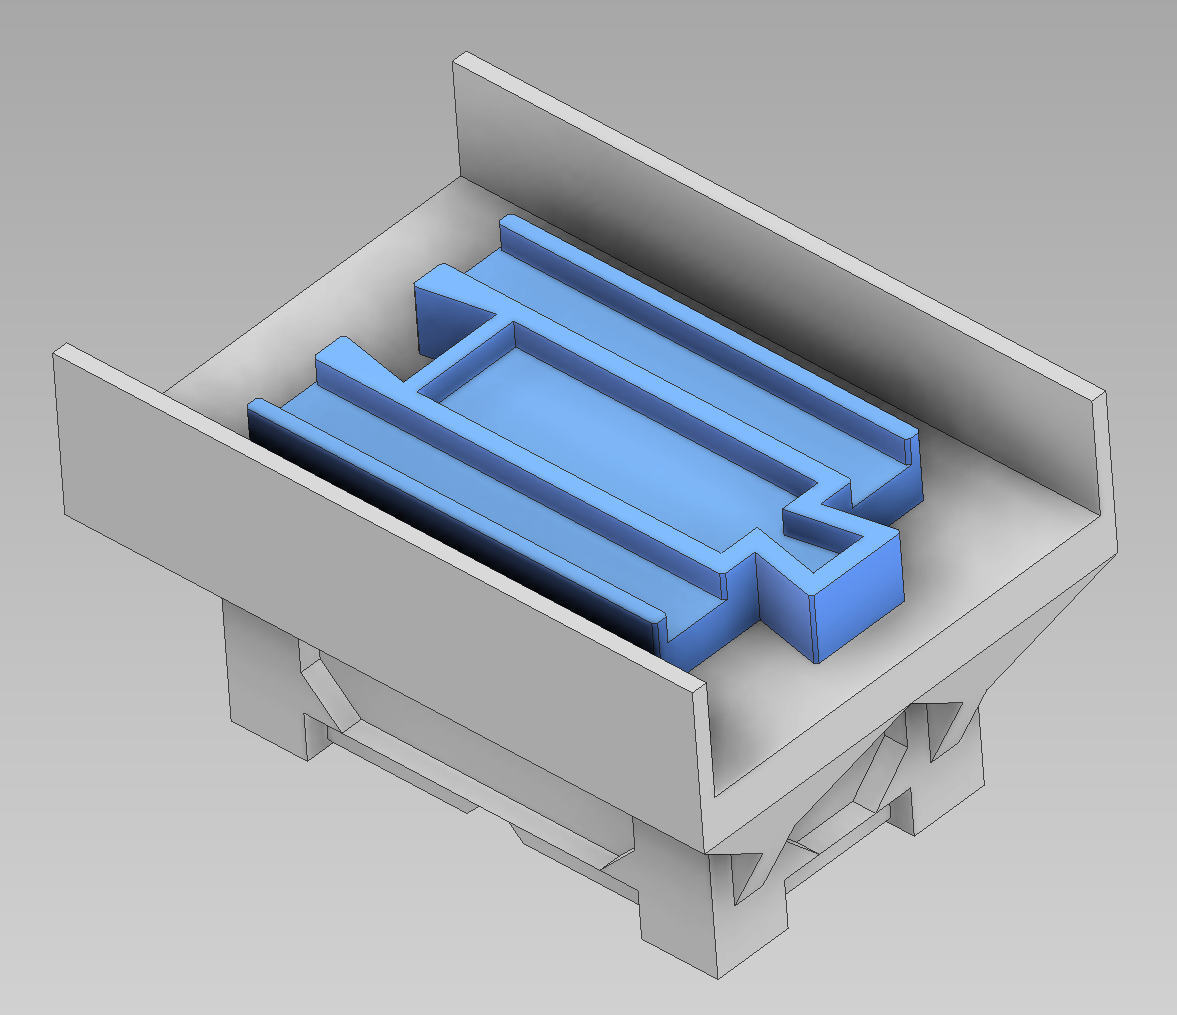
ViaductPillarUnit/Viaduct_HorizontalSingle_C.png
