kumarobo/PlaRails/ViaductPillarUnit/ViaductPillar_SingleSpan_C_1u.png

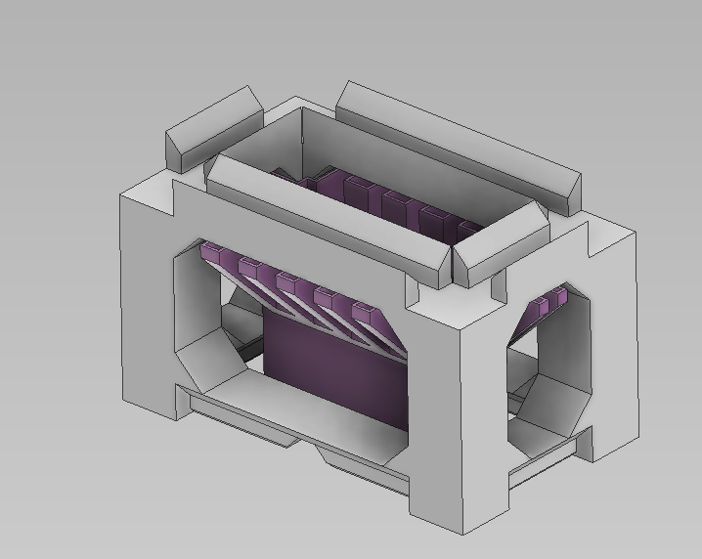
ViaductPillarUnit/ViaductPillar_SingleSpan_C_1u.png
