kumarobo/PlaRails/ViaductPillarUnit/ViaductPillar_SingleSpan_C_05u.png

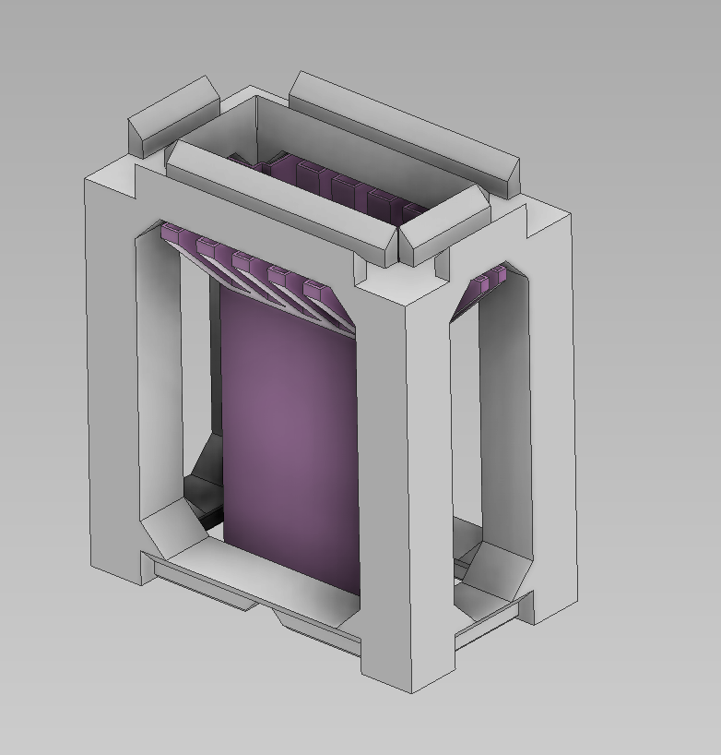
ViaductPillarUnit/ViaductPillar_SingleSpan_C_05u.png
