kumarobo/PlaRails/ViaductPillarUnit/ViaductPillar_SingleSpan_Doublelane_C_05u.png

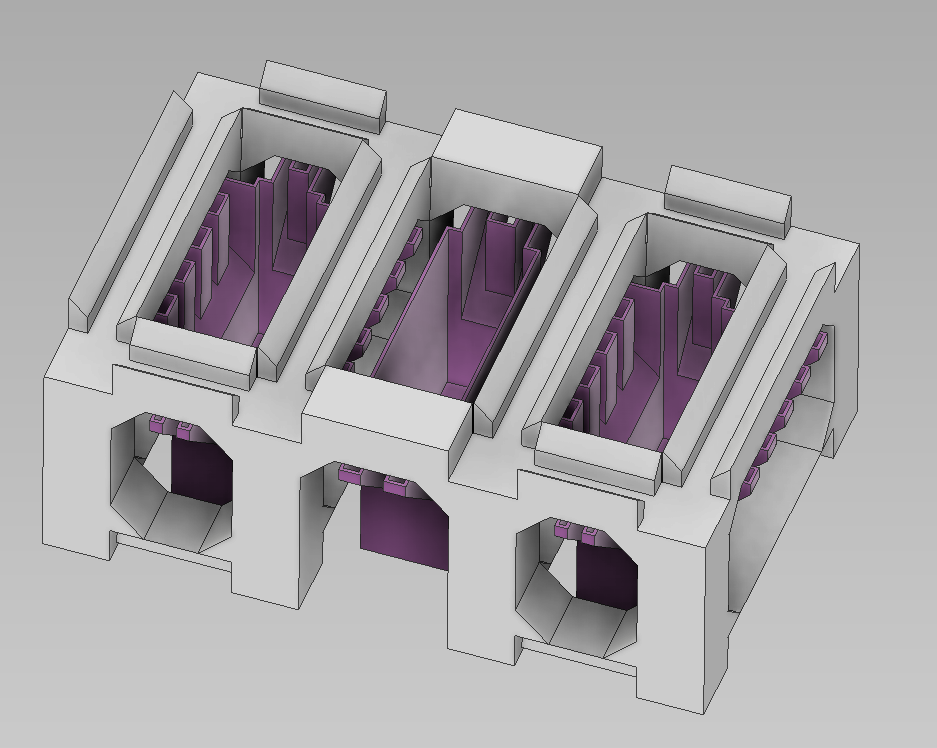
ViaductPillarUnit/ViaductPillar_SingleSpan_Doublelane_C_05u.png
