kumarobo/PlaRails/VPUSlope/Slope_HighEnd_C_FF.png

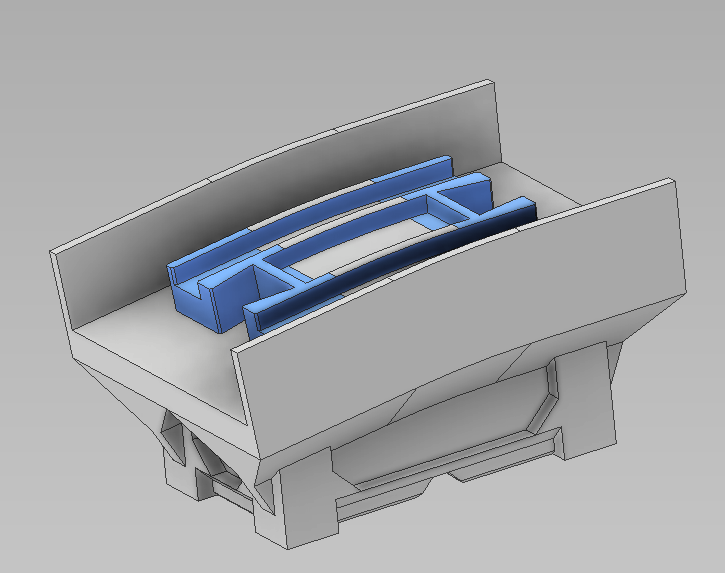
VPUSlope/Slope_HighEnd_C_FF.png
