kumarobo/PlaRails/VPUSlope/Slope_HighEnd_C_FM.png

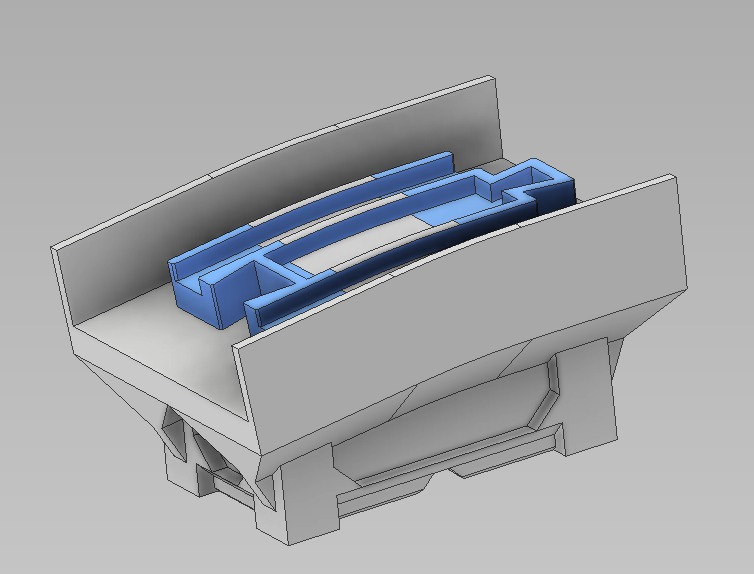
VPUSlope/Slope_HighEnd_C_FM.png
