kumarobo/PlaRails/VPUSlope/Slope_LowEnd_C_FM.png

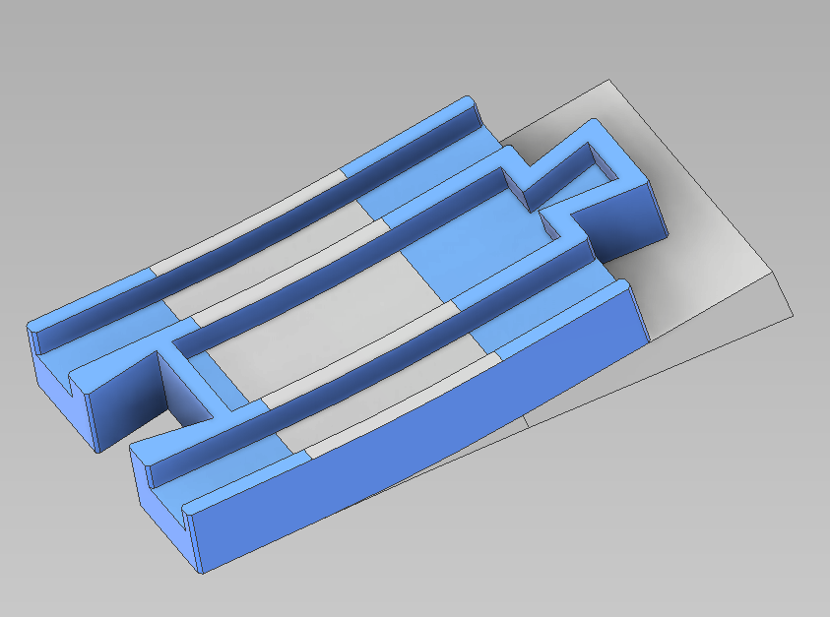
VPUSlope/Slope_LowEnd_C_FM.png
