kumarobo/PlaRails/VPUSlope/Slope_LowEnd_C_MM.png

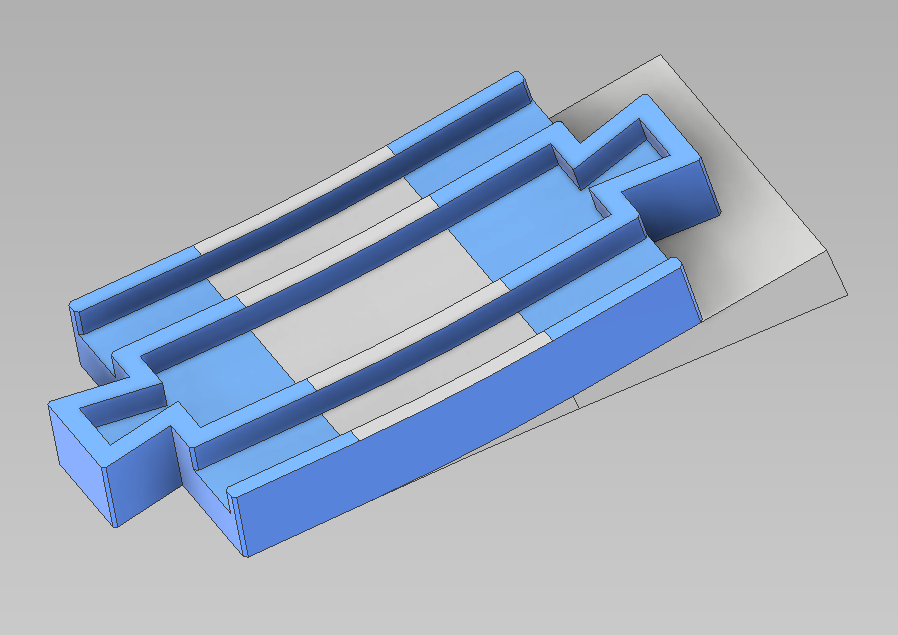
VPUSlope/Slope_LowEnd_C_MM.png
