kumarobo/PlaRails/VPUSlope/Slope_LowEndHi_C_FM.png

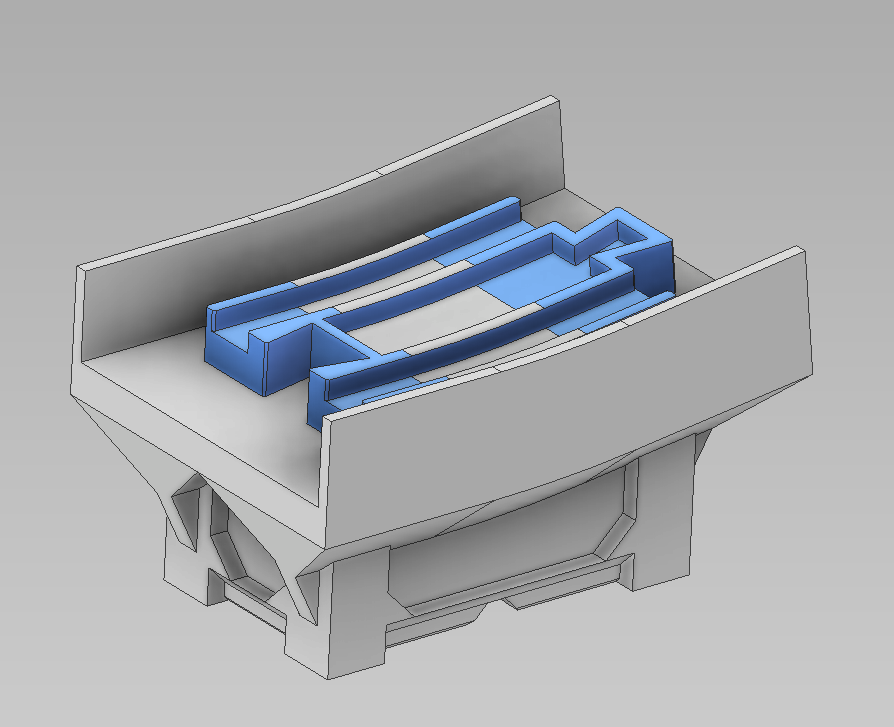
VPUSlope/Slope_LowEndHi_C_FM.png
