kumarobo/PlaRails/VPUSlope/Slope_LowEndHi_C_MM.png

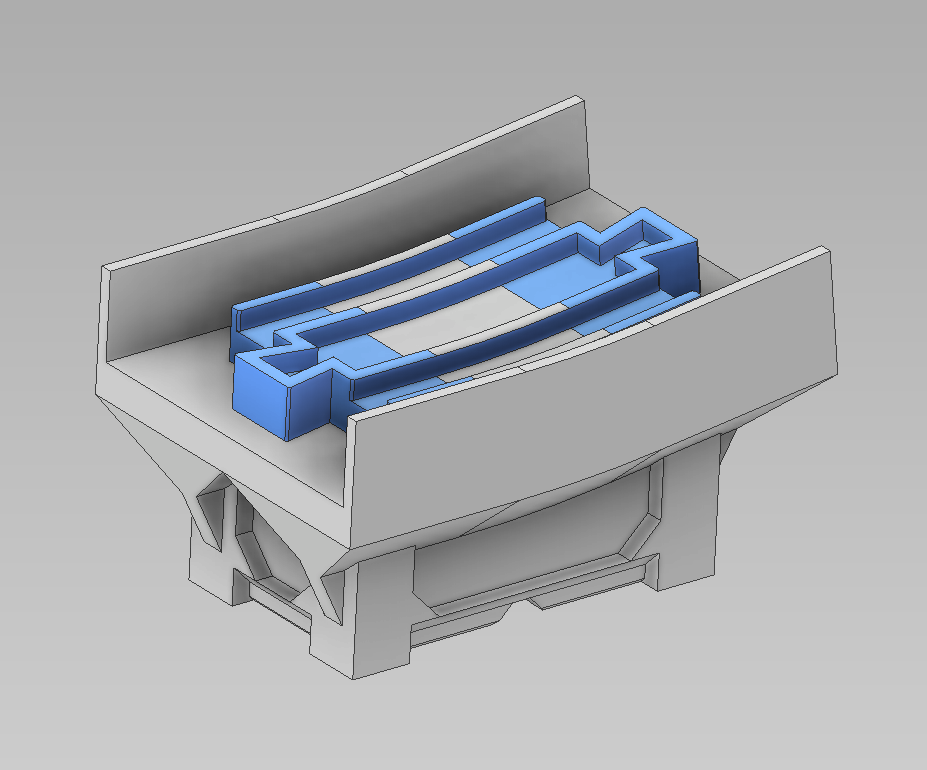
VPUSlope/Slope_LowEndHi_C_MM.png
