kumarobo/PlaRails/VPUSlope/Slope_Middle_C.png

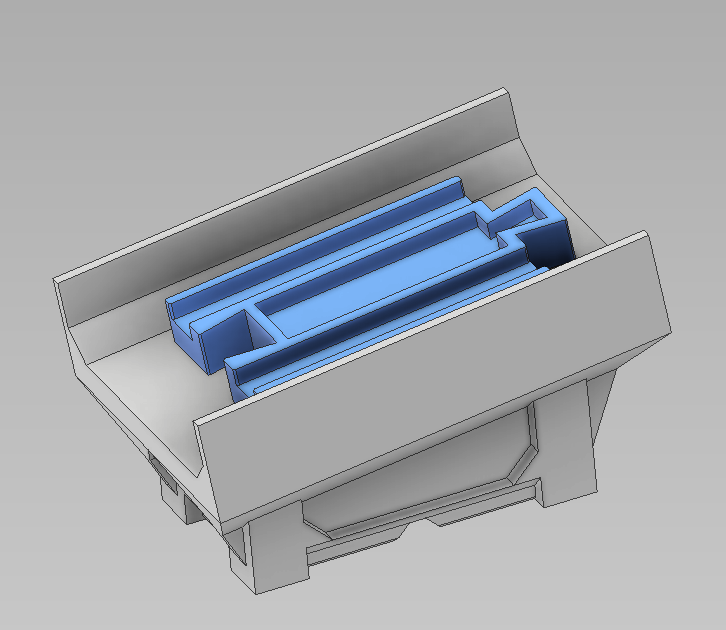
VPUSlope/Slope_Middle_C.png
