kumarobo/PlaRails/StraightRail/StraightRail_C_DSSMF.stl

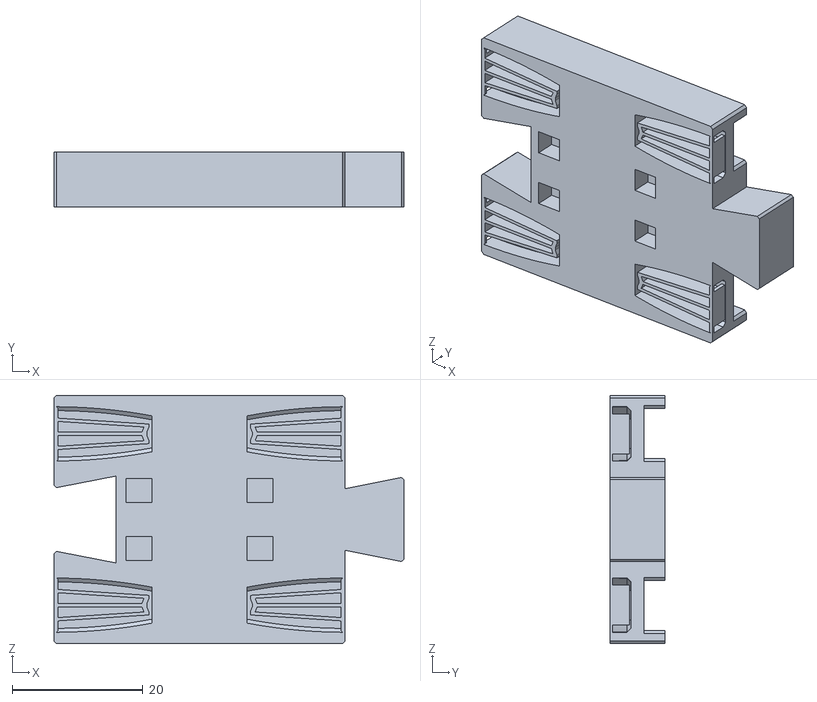
[picture p75: CAD file, 2021-06-13]
StraightRail/StraightRail_C_DSSMF.stl
53.5 x 8.40 x 38.0
