kumarobo/PlaRails/ViaductPillarUnit/ViaductPillar_SingleSpan_C_05u.stl

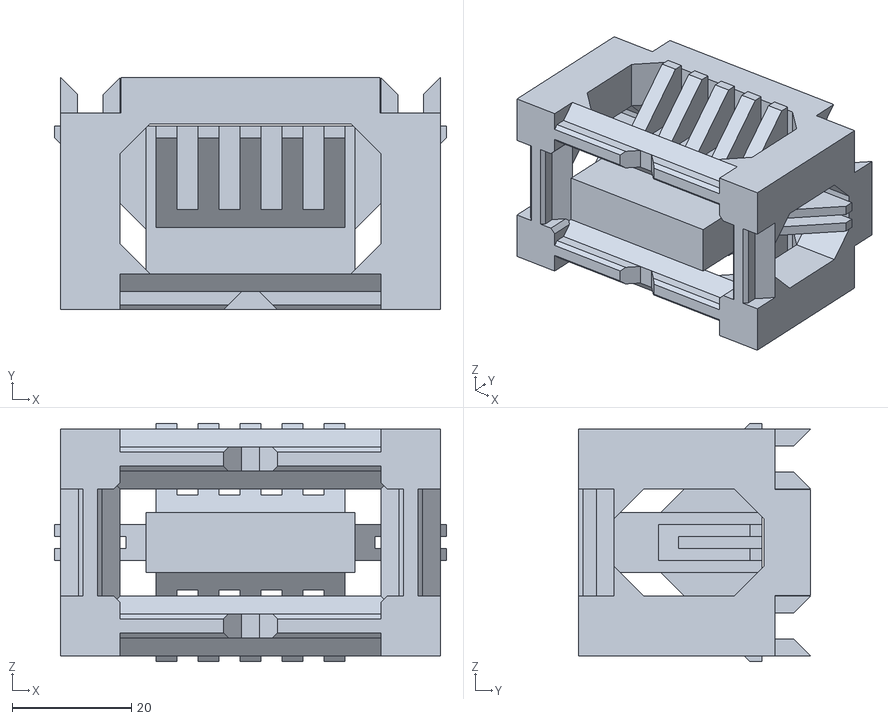
[picture p76: CAD file, 2021-05-15]
ViaductPillarUnit/ViaductPillar_SingleSpan_C_05u.stl
65.8 x 38.9 x 40.0
