kumarobo/PlaRails/VPUSlope/Slope_Middle_C.stl

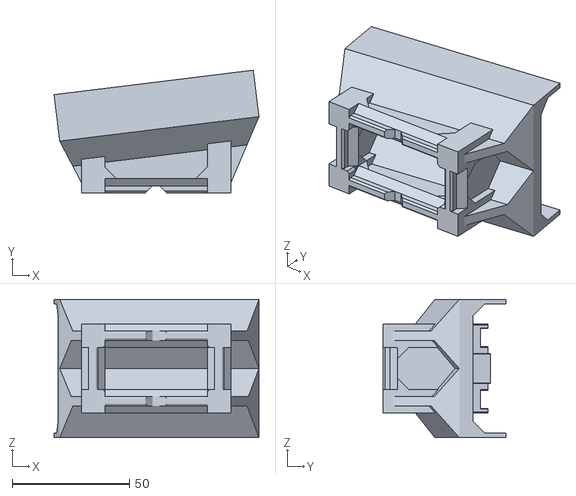
[picture p77: CAD file, 2021-05-15]
VPUSlope/Slope_Middle_C.stl
87.6 x 52.4 x 59.0
