kumarobo/PlaRails/Crossover/RailVCoverCV_S.stl

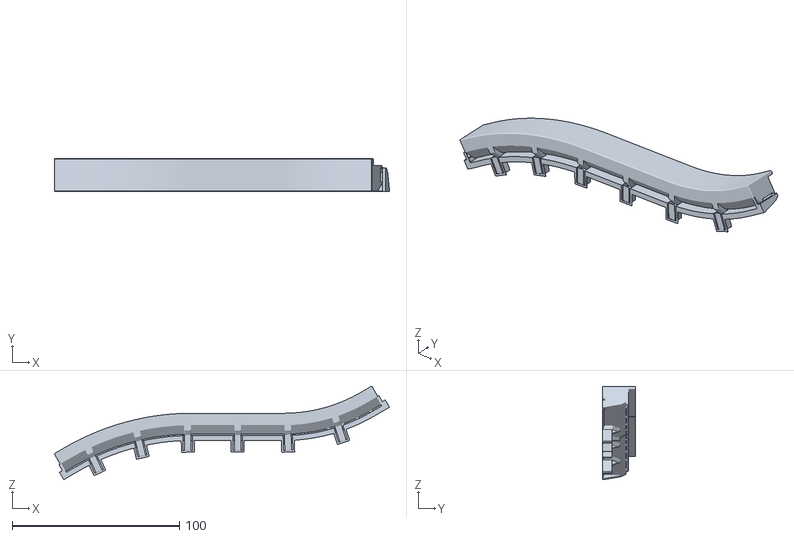
[picture p78: CAD file, 2021-04-25]
Crossover/RailVCoverCV_S.stl
200.6 x 20.0 x 55.9
