kumarobo/PlaRails/CurveRail/CurveRail-215-45.stl

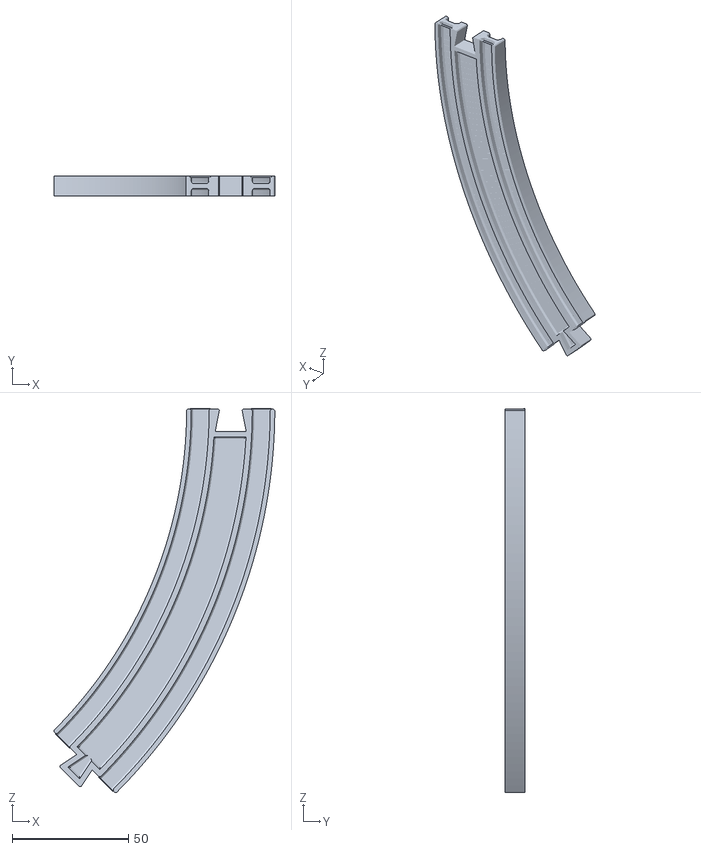
[picture p79: CAD file, 2021-04-18]
CurveRail/CurveRail-215-45.stl
95.1 x 8.40 x 165.4
