kumarobo/PlaRails/DoubleCross/DoubleCross_Rturn_C.stl

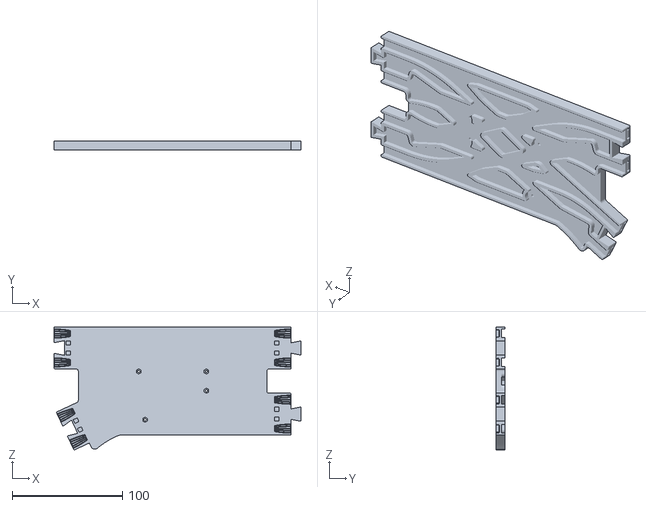
[picture p80: CAD file, 2021-04-25]
DoubleCross/DoubleCross_Rturn_C.stl
224.0 x 8.40 x 111.5
