kumarobo/PlaRails/DoubleSlip/DoubleSlipHR_C_H_H.stl

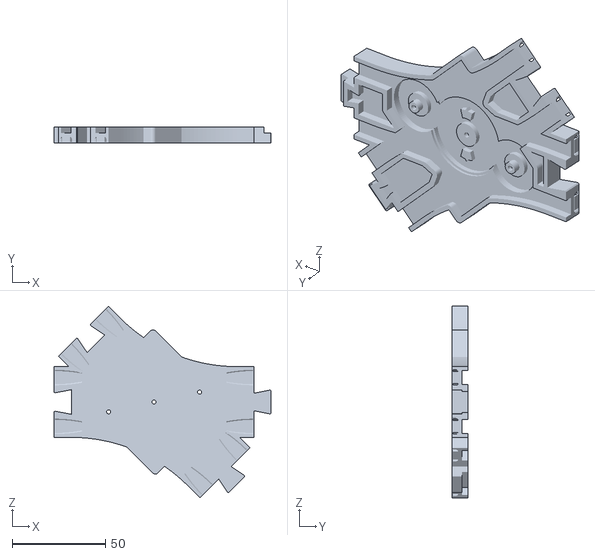
[picture p81: CAD file, 2021-06-13]
DoubleSlip/DoubleSlipHR_C_H_H.stl
116.5 x 8.40 x 102.9
