kumarobo/PlaRails/Misc/AsterMale_8.stl

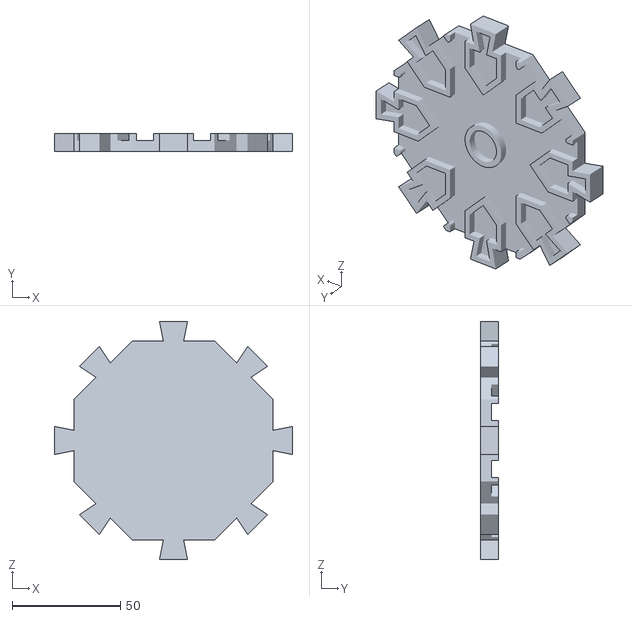
[picture p82: CAD file, 2021-05-15]
Misc/AsterMale_8.stl
109.7 x 8.40 x 109.7
