kumarobo/PlaRails/PocketTrackPoint/PocketPoint_C.stl

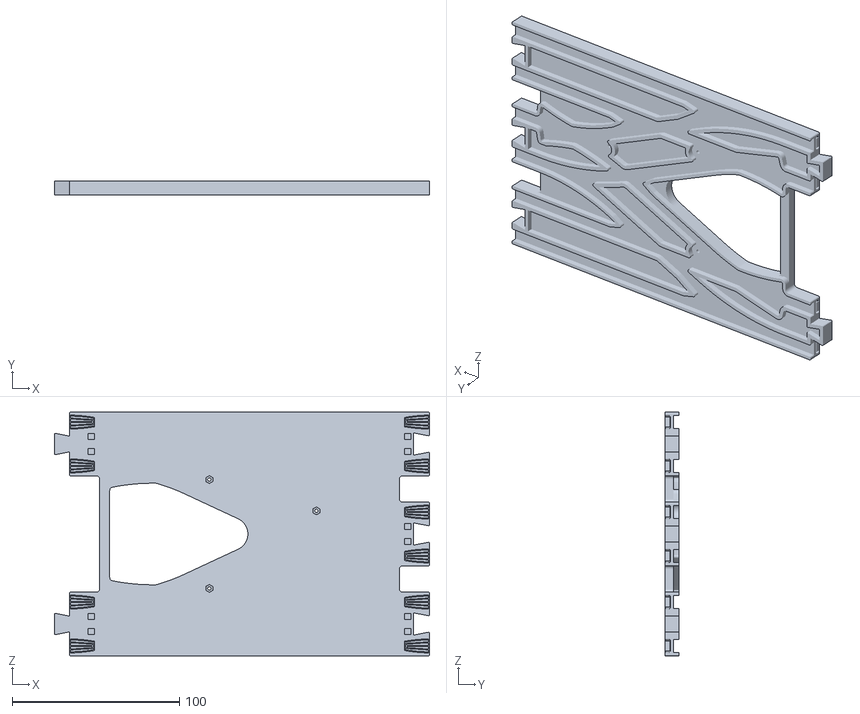
[picture p83: CAD file, 2021-04-19]
PocketTrackPoint/PocketPoint_C.stl
224.0 x 8.40 x 145.5
