kumarobo/PlaRails/RealRails/RR_SingleTurnout_SB_C.stp

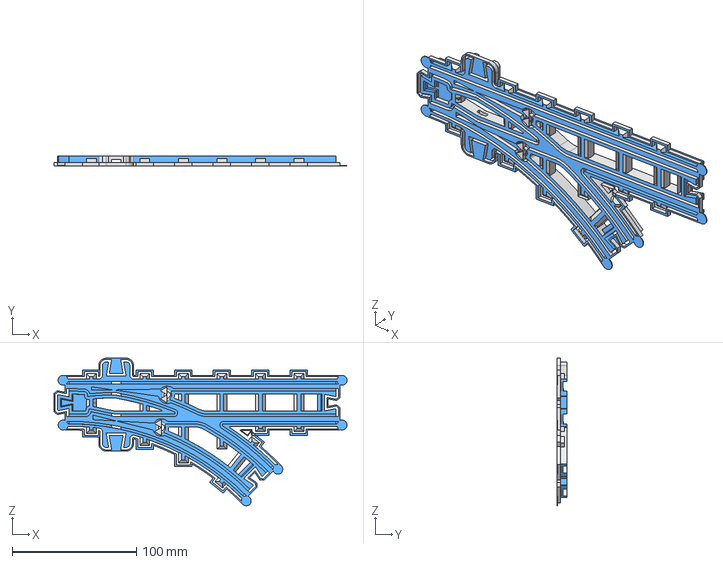
[picture p84: CAD file, 2025-03-15]
RealRails/RR_SingleTurnout_SB_C.stp
235.7 x 8.40 x 118.8 mm
