kumarobo/PlaRails/ShiftRail/ShiftRail_S_1L_HDL32.stl

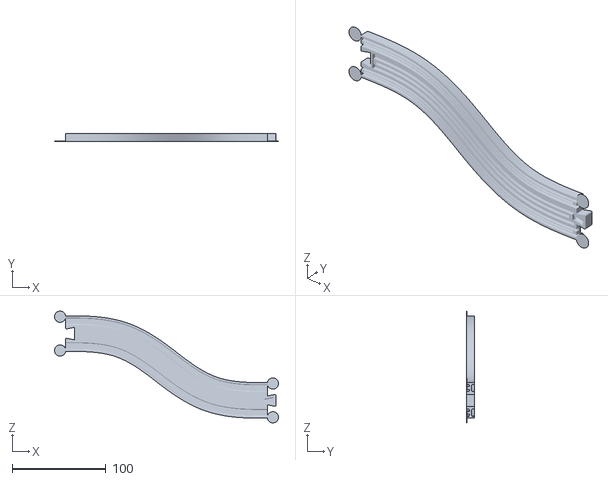
[picture p85: CAD file, 2021-06-13]
ShiftRail/ShiftRail_S_1L_HDL32.stl
238.8 x 8.40 x 119.2
