kumarobo/PlaRails/SimpleSlope/Slope_HighEnd_C.stl

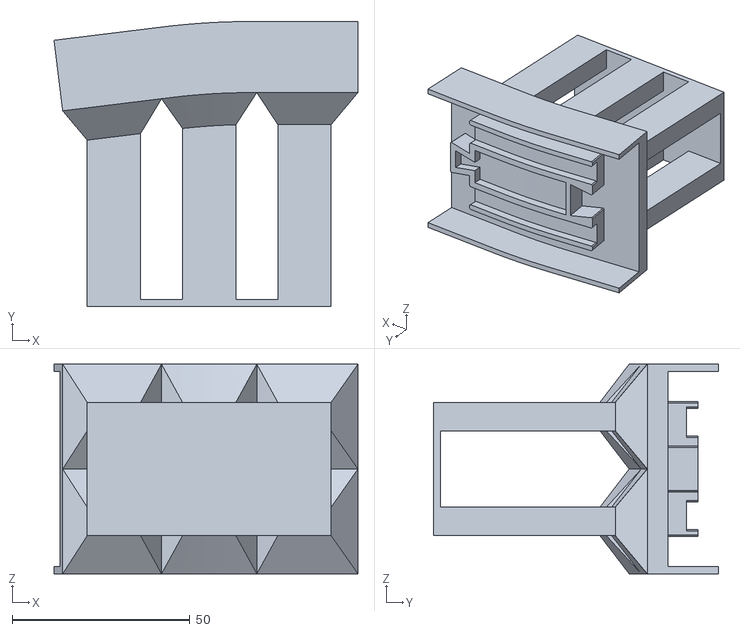
[picture p86: CAD file, 2021-04-25]
SimpleSlope/Slope_HighEnd_C.stl
85.5 x 80.2 x 59.0
