kumarobo/PlaRails/StraightRail/StraightRail_C_60MM.stl

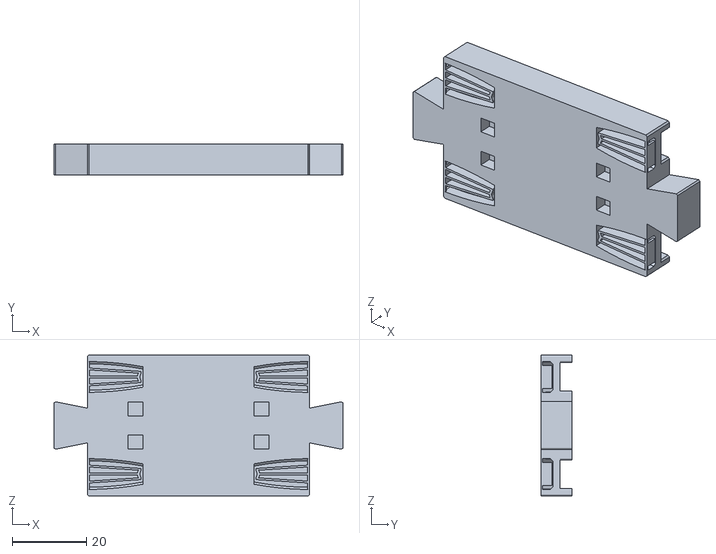
[picture p87: CAD file, 2021-04-18]
StraightRail/StraightRail_C_60MM.stl
78.0 x 8.40 x 38.0
