kumarobo/PlaRails/TrussCC/TrussCC_box.stl

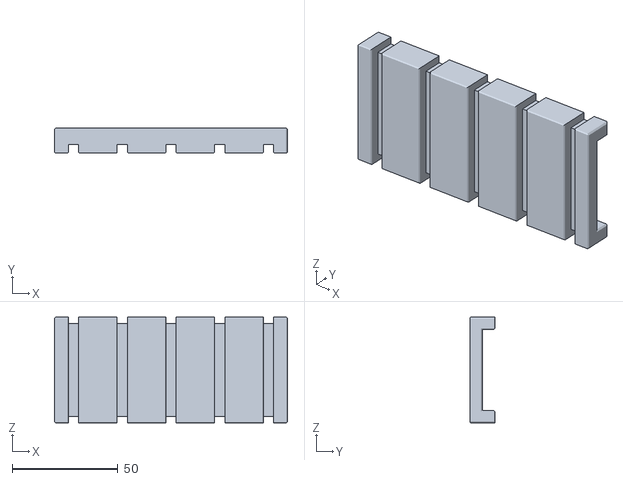
[picture p88: CAD file, 2021-04-21]
TrussCC/TrussCC_box.stl
110.0 x 12.0 x 50.0
