kumarobo/PlaRails/ViaductPillar/StandardPillarCover.stl

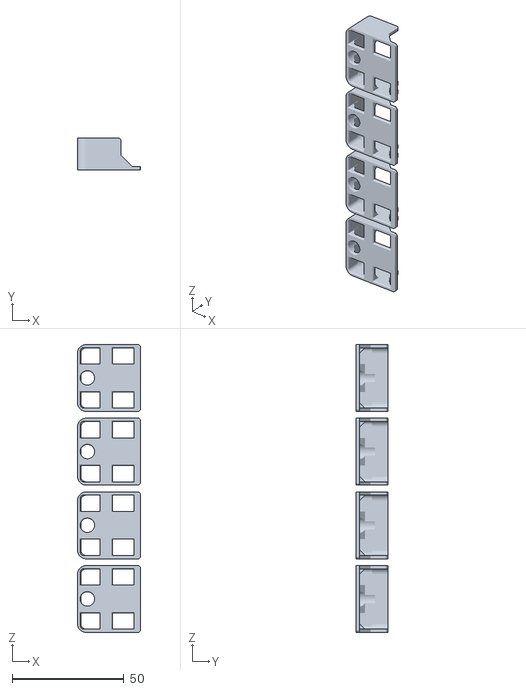
[picture p89: CAD file, 2021-04-21]
ViaductPillar/StandardPillarCover.stl
28.3 x 14.2 x 129.0
