kumarobo/PlaRails/ViaductPillarUnit/ViaductPillar_SingleSpan_Doublelane_C_05u.stl

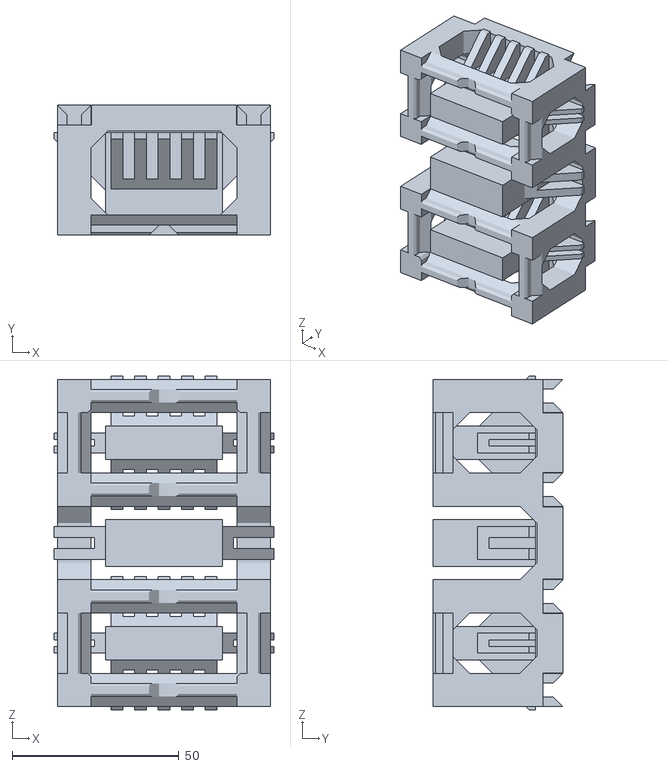
[picture p90: CAD file, 2021-05-15]
ViaductPillarUnit/ViaductPillar_SingleSpan_Doublelane_C_05u.stl
65.8 x 39.0 x 100.0
