kumarobo/PlaRails/VPUSlope/Slope_LowEnd_C.stl

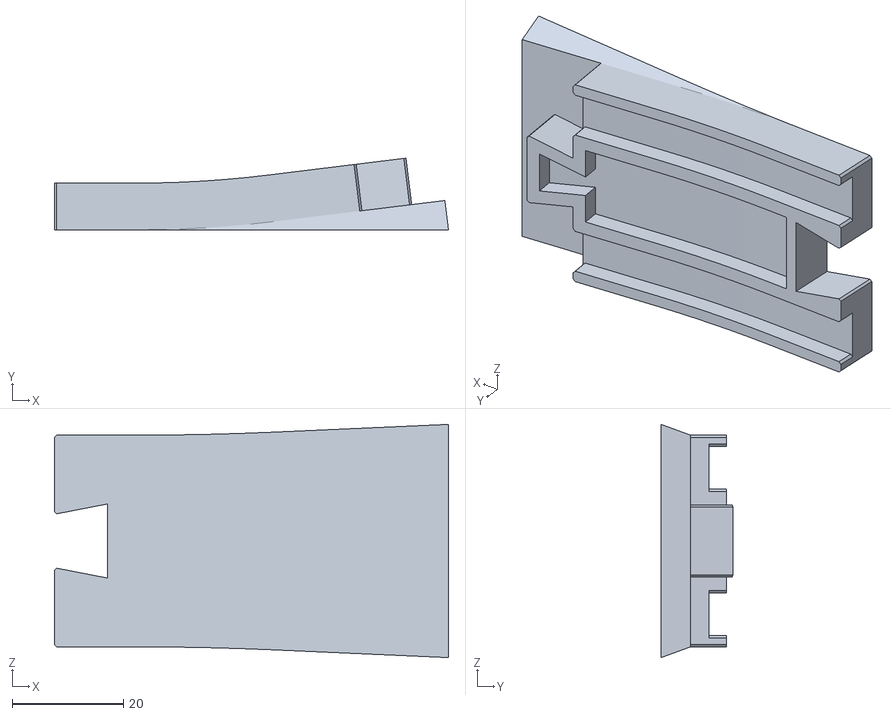
[picture p91: CAD file, 2021-05-15]
VPUSlope/Slope_LowEnd_C.stl
70.7 x 12.9 x 41.9
