kumarobo/PlaRails/Crossover/SingleCrossBar.stl

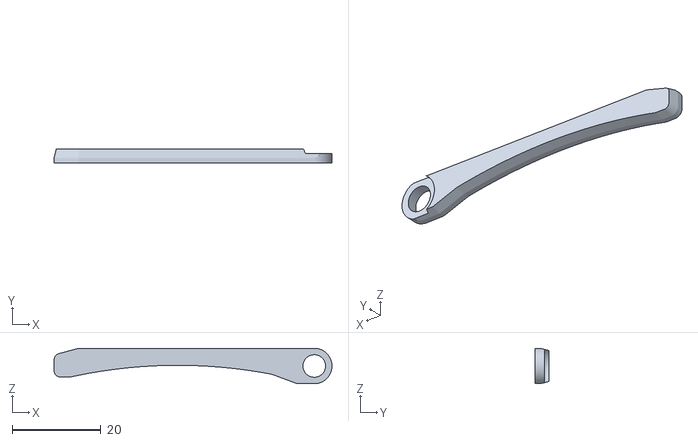
[picture p92: CAD file, 2021-04-25]
Crossover/SingleCrossBar.stl
62.7 x 3.20 x 8.00
