kumarobo/PlaRails/CurveRail/CurveRail-89-25.stl

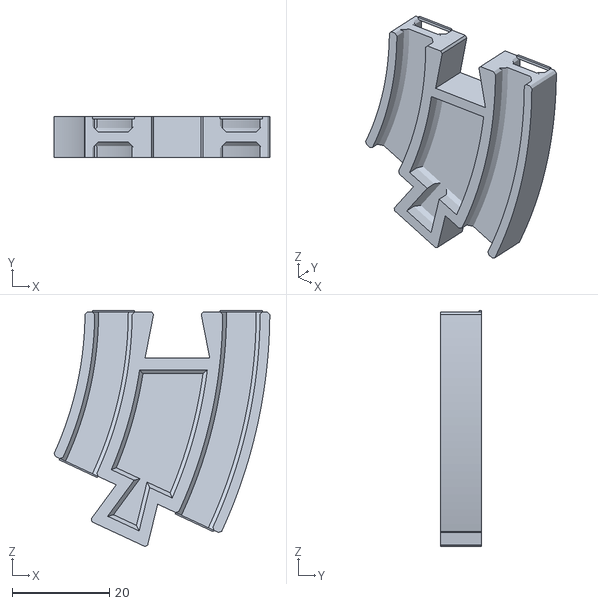
[picture p93: CAD file, 2021-04-18]
CurveRail/CurveRail-89-25.stl
44.3 x 8.40 x 48.5
