kumarobo/PlaRails/DoubleCross/DoubleCross_Straight_C.stl

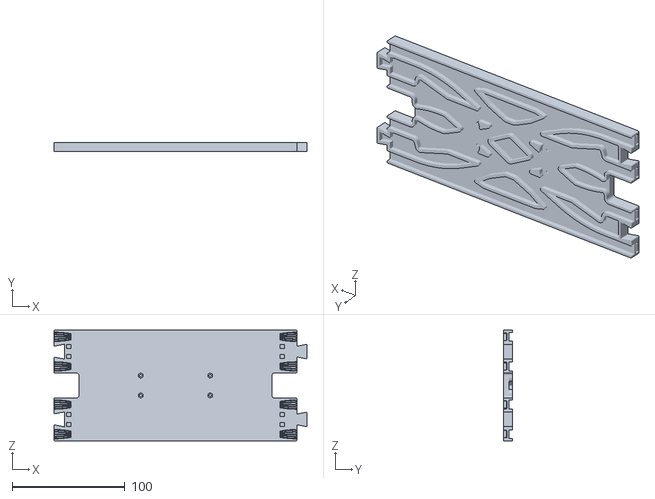
[picture p94: CAD file, 2021-04-25]
DoubleCross/DoubleCross_Straight_C.stl
224.0 x 8.40 x 98.0
