kumarobo/PlaRails/DoubleSlip/DoubleSlipHR_C_HS_H.stl

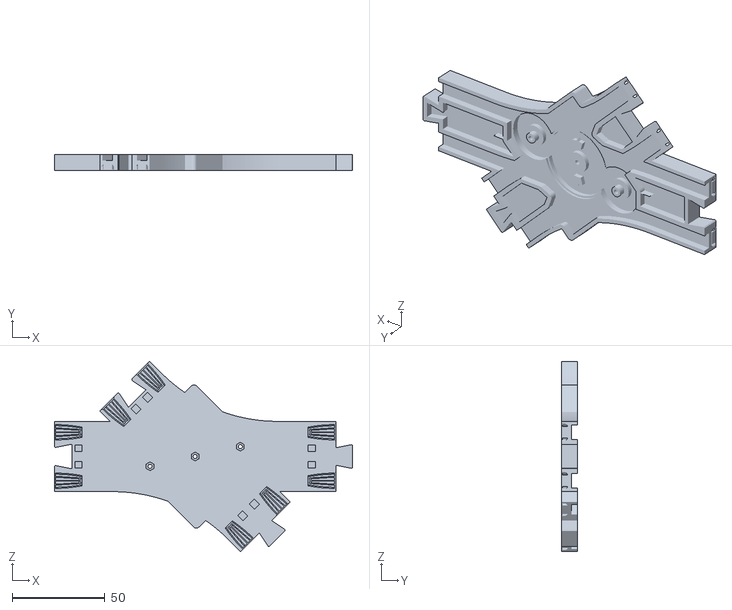
[picture p95: CAD file, 2021-05-24]
DoubleSlip/DoubleSlipHR_C_HS_H.stl
161.0 x 8.40 x 102.9
