kumarobo/PlaRails/Misc/AsterMale_6.stl

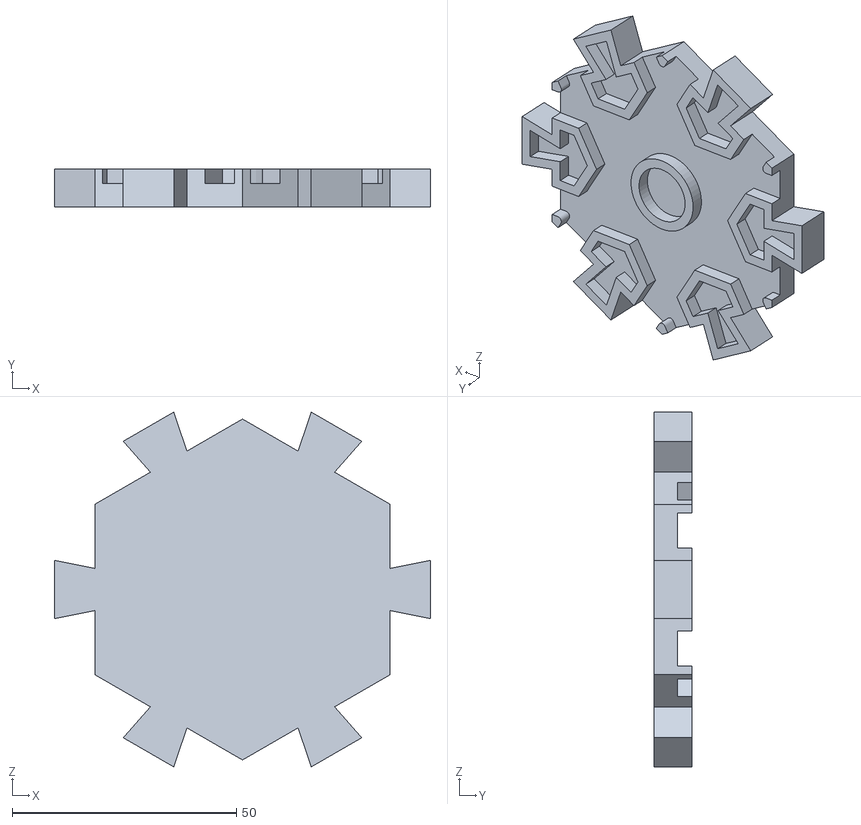
[picture p96: CAD file, 2021-05-15]
Misc/AsterMale_6.stl
83.8 x 8.40 x 79.1
