kumarobo/PlaRails/RealRails/RR_ThreeWay_SB_C.stp

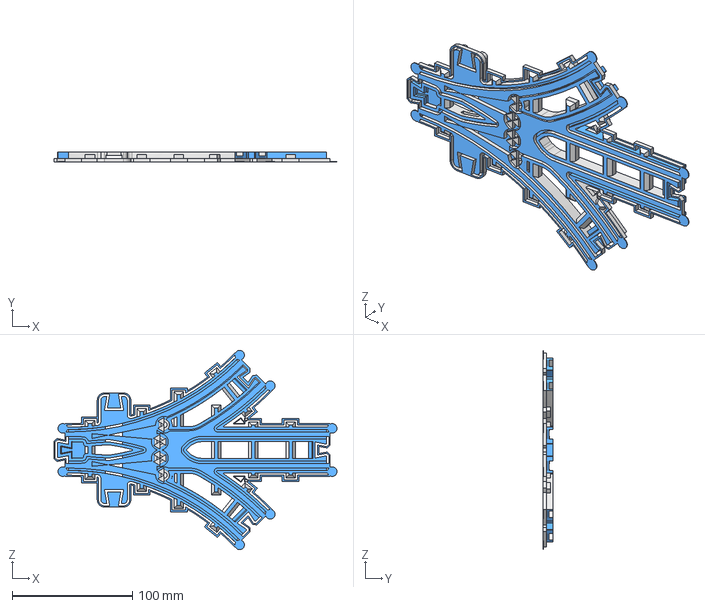
[picture p97: CAD file, 2025-03-15]
RealRails/RR_ThreeWay_SB_C.stp
235.7 x 8.40 x 166.0 mm
