kumarobo/PlaRails/StraightRail/StraightRail_C_134MF.stl

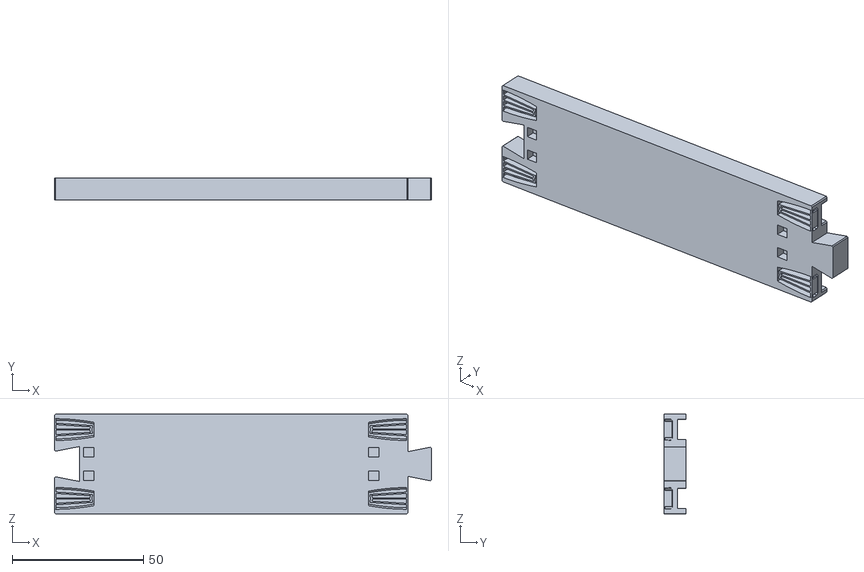
[picture p98: CAD file, 2021-04-18]
StraightRail/StraightRail_C_134MF.stl
143.5 x 8.40 x 38.0
