kumarobo/PlaRails/ViaductPillarUnit/Viaduct_HorizontalSingle_C.stl

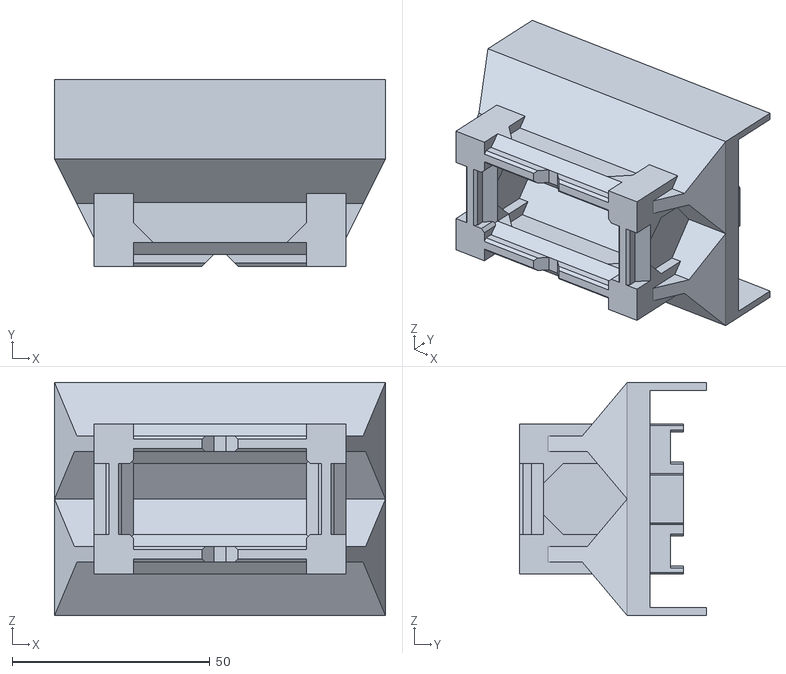
[picture p99: CAD file, 2021-05-15]
ViaductPillarUnit/Viaduct_HorizontalSingle_C.stl
83.8 x 47.2 x 59.0
