kumarobo/PlaRails/VPUSlope/Slope_HighEnd_C_FF.stl

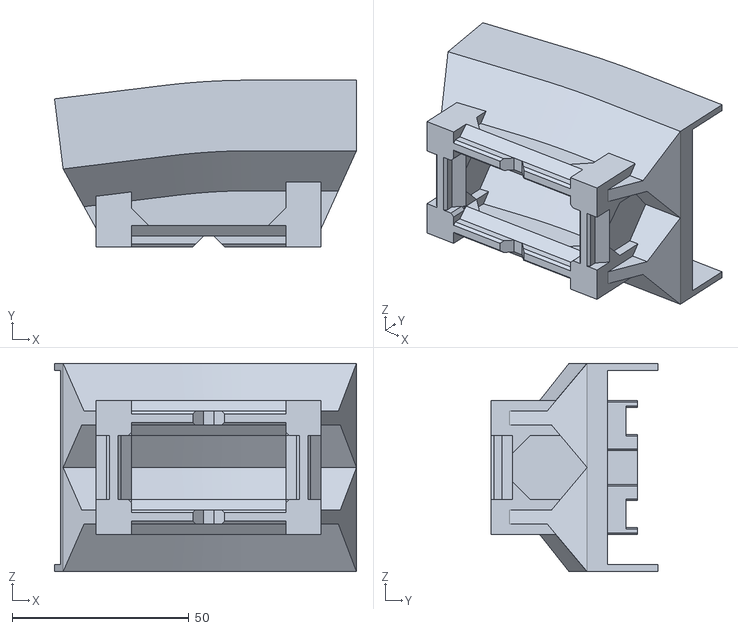
[picture p100: CAD file, 2021-05-15]
VPUSlope/Slope_HighEnd_C_FF.stl
85.5 x 47.2 x 59.0
