kumarobo/PlaRails/Crossover/SingleCrossoverIA_Cross.stl

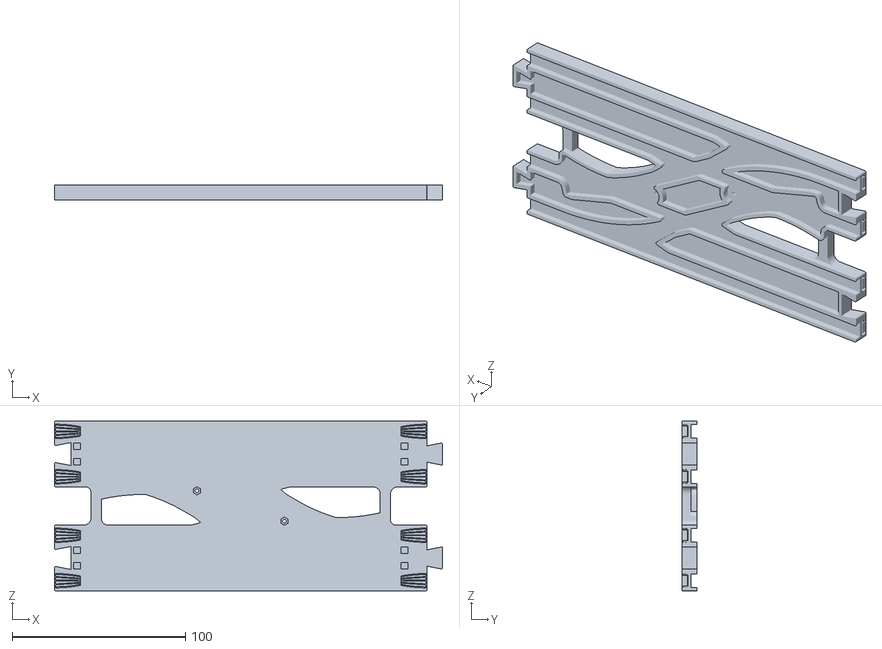
[picture p101: CAD file, 2021-04-25]
Crossover/SingleCrossoverIA_Cross.stl
224.0 x 8.40 x 98.0
