kumarobo/PlaRails/CurveRail/CurveRail-215half-90.stl

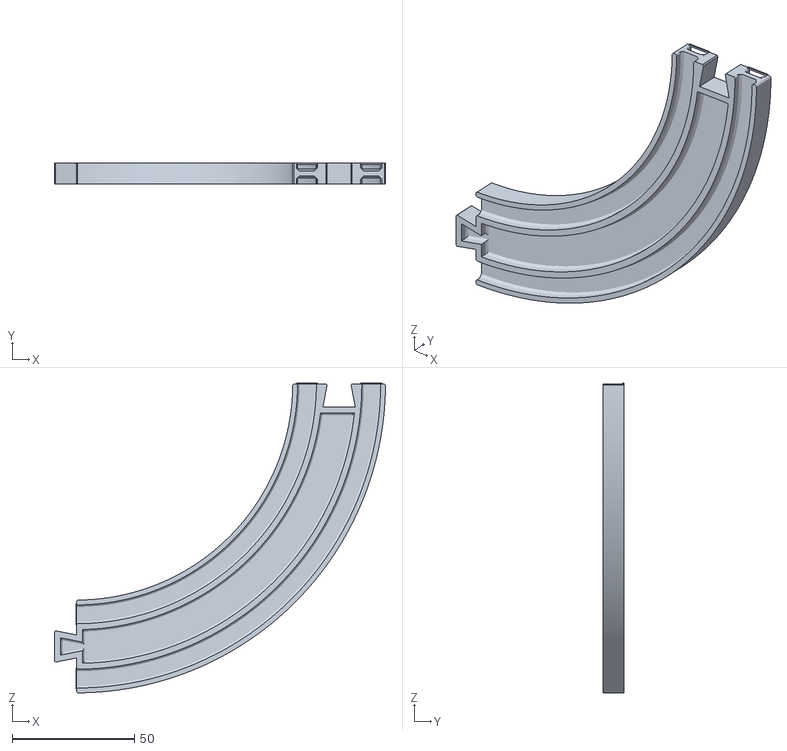
[picture p102: CAD file, 2021-04-18]
CurveRail/CurveRail-215half-90.stl
135.5 x 8.40 x 126.8
