kumarobo/PlaRails/DoubleSlip/DoubleSlipHR_C_H_HS.stl

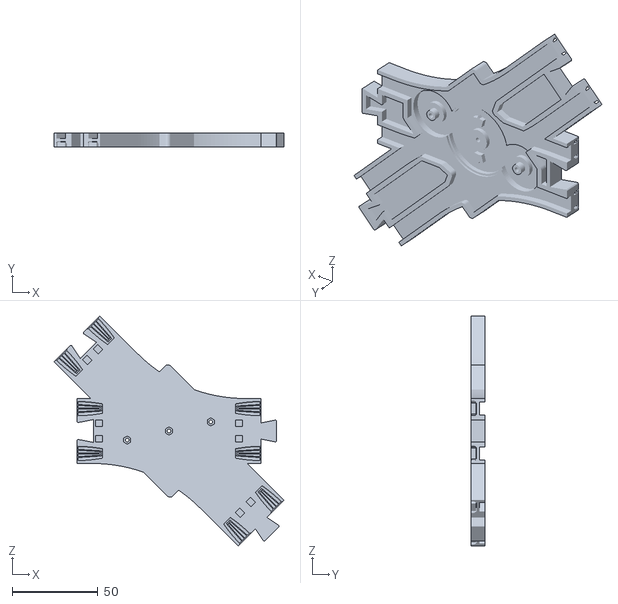
[picture p103: CAD file, 2021-05-24]
DoubleSlip/DoubleSlipHR_C_H_HS.stl
134.4 x 8.40 x 134.4
