kumarobo/PlaRails/RealRails/RR_ThreeWay_CA.stl

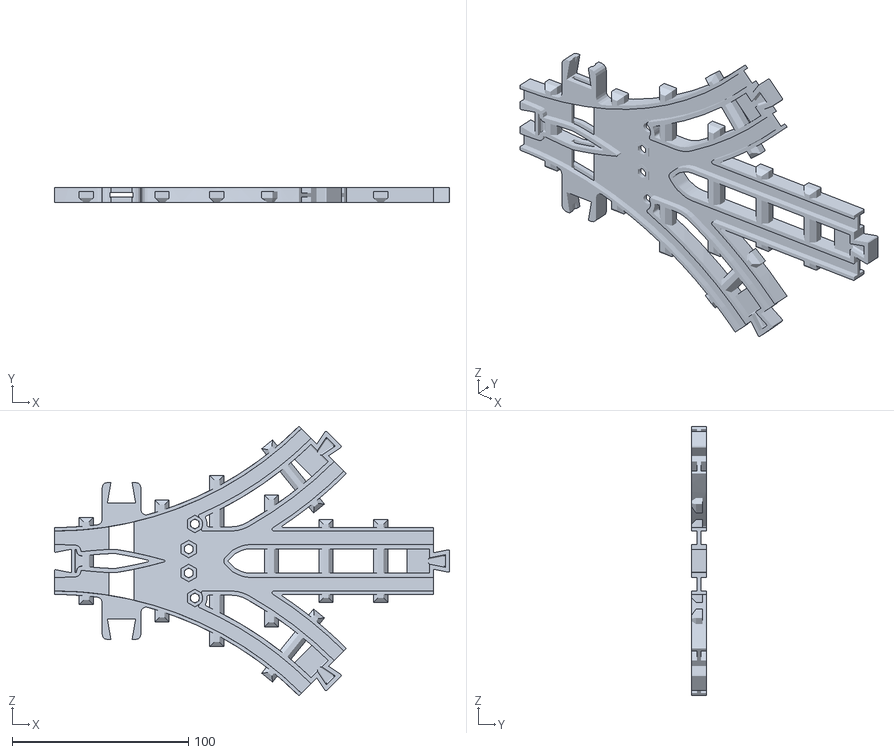
[picture p104: CAD file, 2025-03-15]
RealRails/RR_ThreeWay_CA.stl
224.0 x 8.40 x 152.8
