kumarobo/PlaRails/ShiftRail/ShiftRail_S_34L_HLD.stl

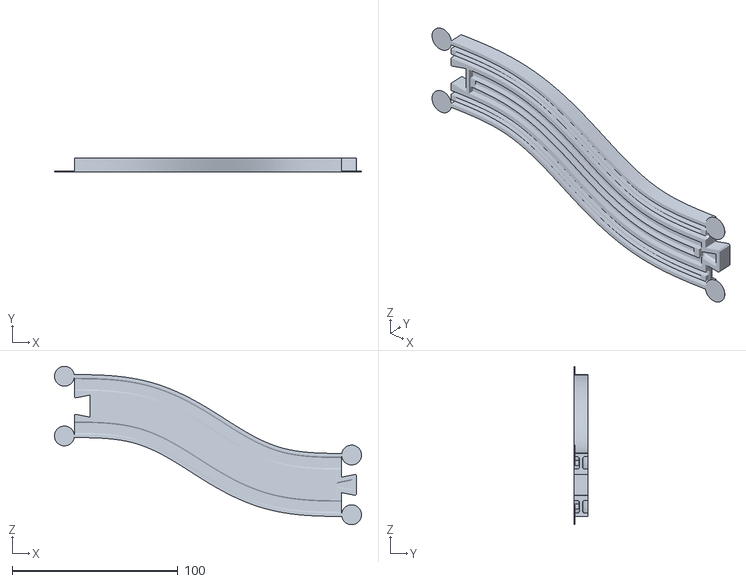
[picture p105: CAD file, 2021-06-13]
ShiftRail/ShiftRail_S_34L_HLD.stl
185.1 x 8.40 x 95.5
