kumarobo/PlaRails/StraightRail/StraightRail_C_26FF.stl

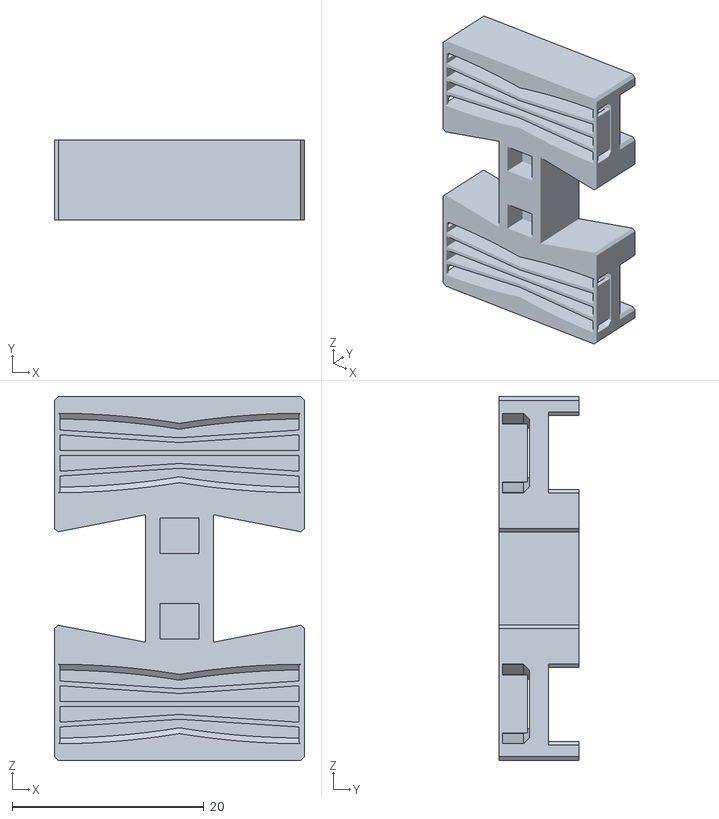
[picture p106: CAD file, 2021-04-18]
StraightRail/StraightRail_C_26FF.stl
26.1 x 8.40 x 38.0
