kumarobo/PlaRails/ViaductPillarUnit/ViaductPillar_SingleSpan_C_1u.stl

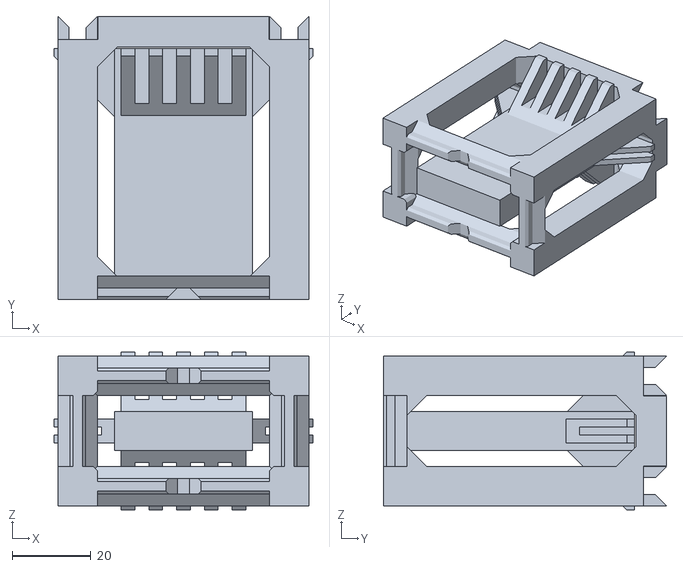
[picture p107: CAD file, 2021-05-15]
ViaductPillarUnit/ViaductPillar_SingleSpan_C_1u.stl
65.8 x 71.9 x 40.0
