kumarobo/PlaRails/Crossover/SingleCrossoverIA_PointA.stl

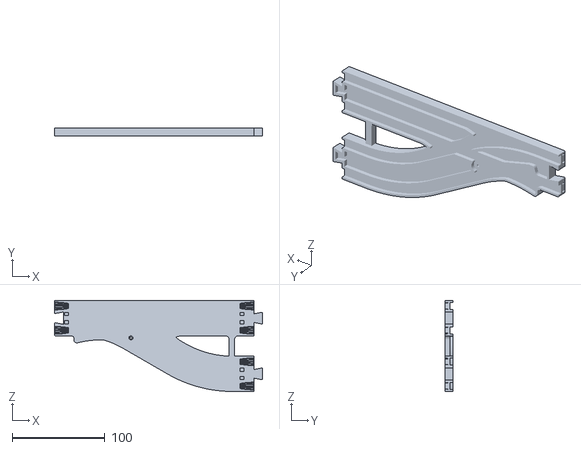
[picture p108: CAD file, 2021-04-25]
Crossover/SingleCrossoverIA_PointA.stl
224.0 x 8.40 x 98.0
