kumarobo/PlaRails/CurveRail/CurveRail-215half-45.stl

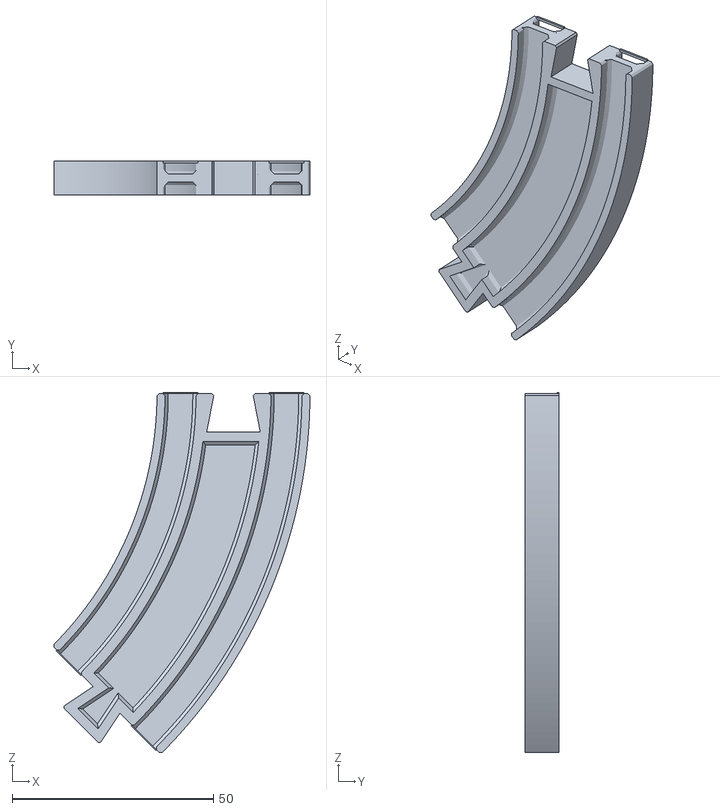
[picture p109: CAD file, 2021-04-18]
CurveRail/CurveRail-215half-45.stl
63.6 x 8.40 x 89.4
