kumarobo/PlaRails/RealRails/RR_ThreeWay_CB.stl

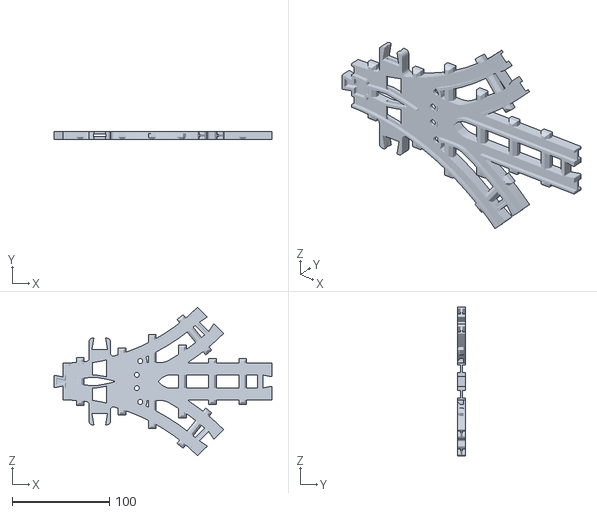
[picture p110: CAD file, 2025-03-15]
RealRails/RR_ThreeWay_CB.stl
224.0 x 8.40 x 152.8
