kumarobo/PlaRails/StraightRail/StraightRail_C_26MM.stl

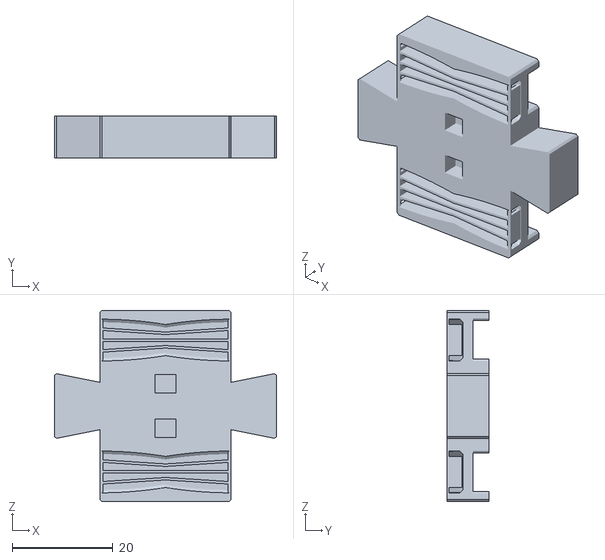
[picture p111: CAD file, 2021-04-18]
StraightRail/StraightRail_C_26MM.stl
44.1 x 8.40 x 38.0
