kumarobo/PlaRails/VPUSlope/Slope_LowEndHi_C_MM.stl

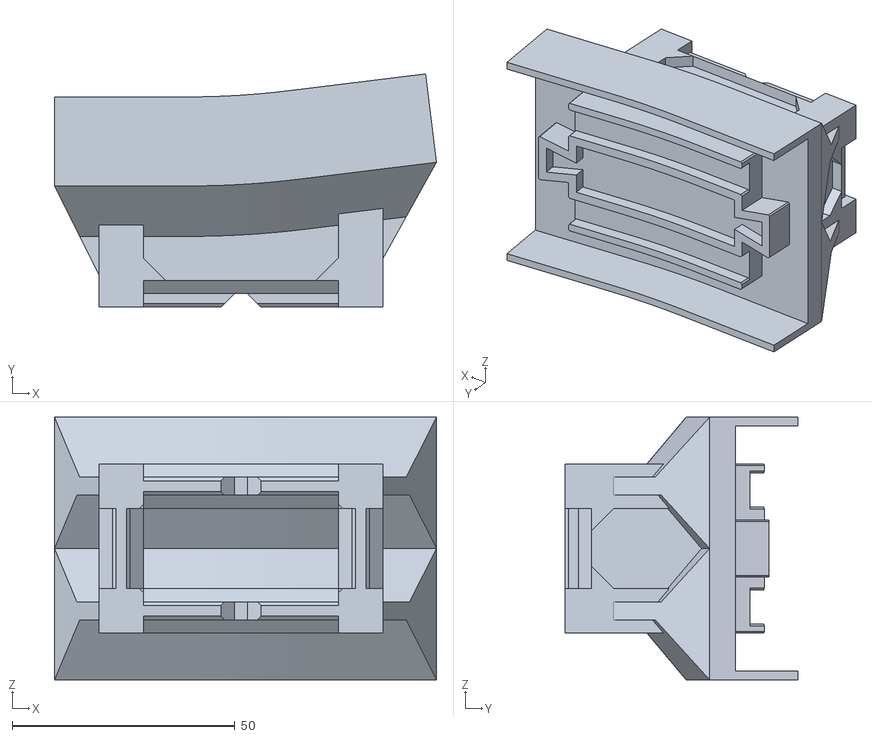
[picture p112: CAD file, 2021-05-15]
VPUSlope/Slope_LowEndHi_C_MM.stl
85.8 x 52.4 x 59.0
