kumarobo/PlaRails/RealRails/RR_ThreeWay_SA_C.stp

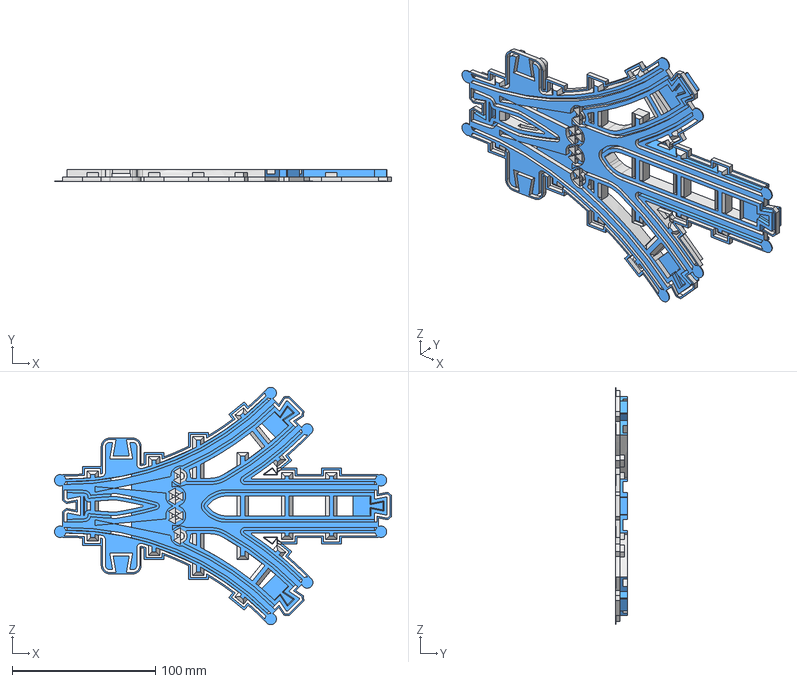
[picture p113: CAD file, 2025-03-15]
RealRails/RR_ThreeWay_SA_C.stp
235.6 x 8.40 x 166.0 mm
