kumarobo/PlaRails/VPUSlope/Slope_LowEnd_C_MM.stl

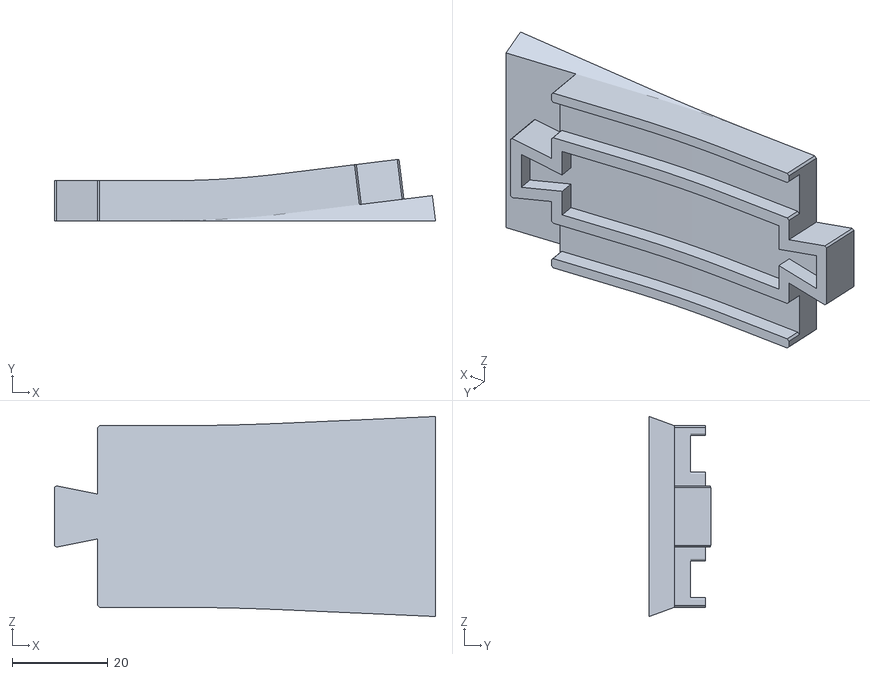
[picture p114: CAD file, 2021-05-15]
VPUSlope/Slope_LowEnd_C_MM.stl
79.7 x 12.9 x 41.9
