kumarobo/PlaRails/RealRails/RR_SingleTurnout_CA.stl

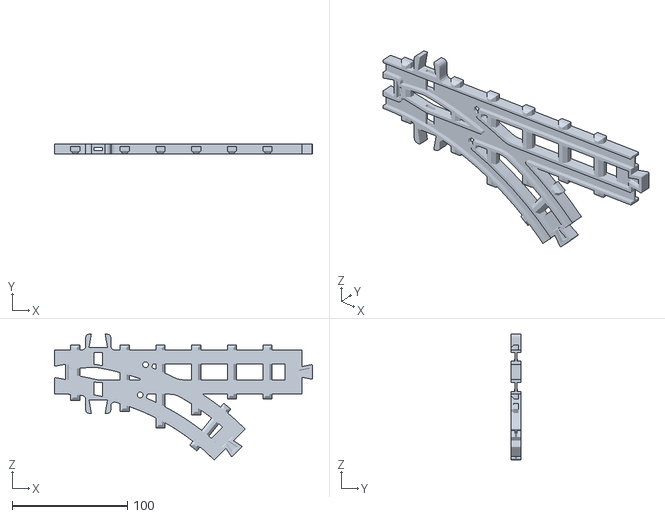
[picture p115: CAD file, 2025-03-15]
RealRails/RR_SingleTurnout_CA.stl
224.0 x 8.40 x 109.2
