kumarobo/PlaRails/RealRails/SwitchLeverUnit_Slider.stp

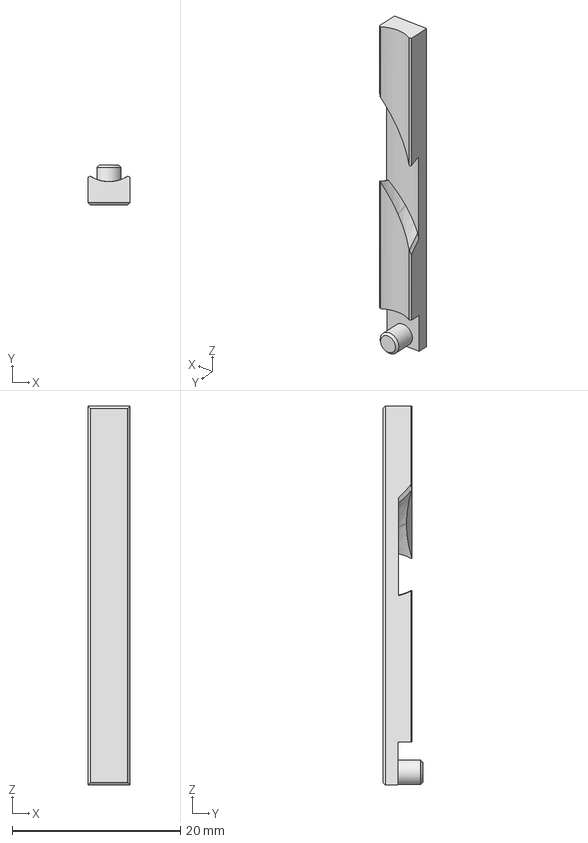
[picture p116: CAD file, 2025-03-15]
RealRails/SwitchLeverUnit_Slider.stp
5.00 x 4.80 x 45.0 mm
