kumarobo/PlaRails/RealRails/RR_SingleTurnoutLever.stp

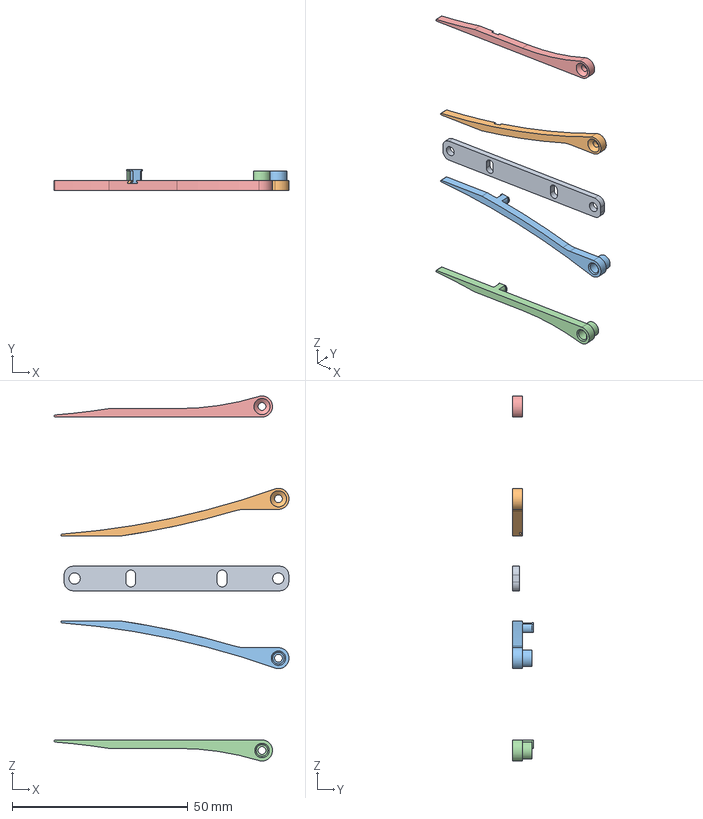
[picture p117: CAD file, 2025-03-15]
RealRails/RR_SingleTurnoutLever.stp
66.9 x 6.00 x 104.0 mm
