kumarobo/PlaRails/Crossover/RailVCoverST_S.stl

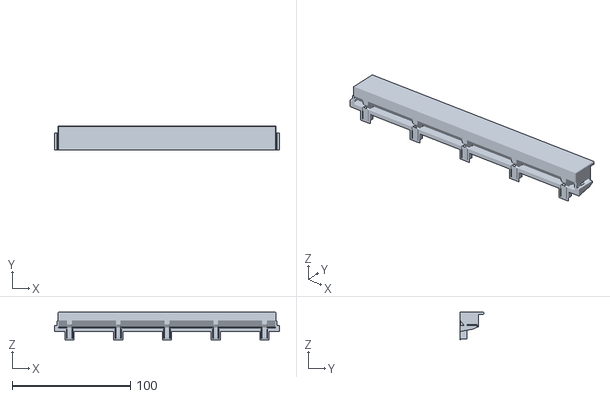
[picture p118: CAD file, 2021-04-25]
Crossover/RailVCoverST_S.stl
190.6 x 20.0 x 23.3
