kumarobo/PlaRails/RealRails/RR_SingleTurnout_CB.stl

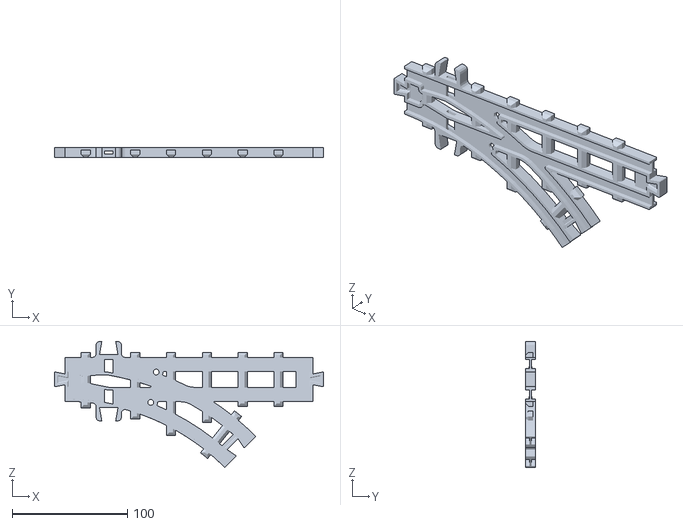
[picture p119: CAD file, 2025-03-15]
RealRails/RR_SingleTurnout_CB.stl
233.0 x 8.40 x 109.2
