kumarobo/PlaRails/RealRails/SwitchLeverUnit_Roller.stp

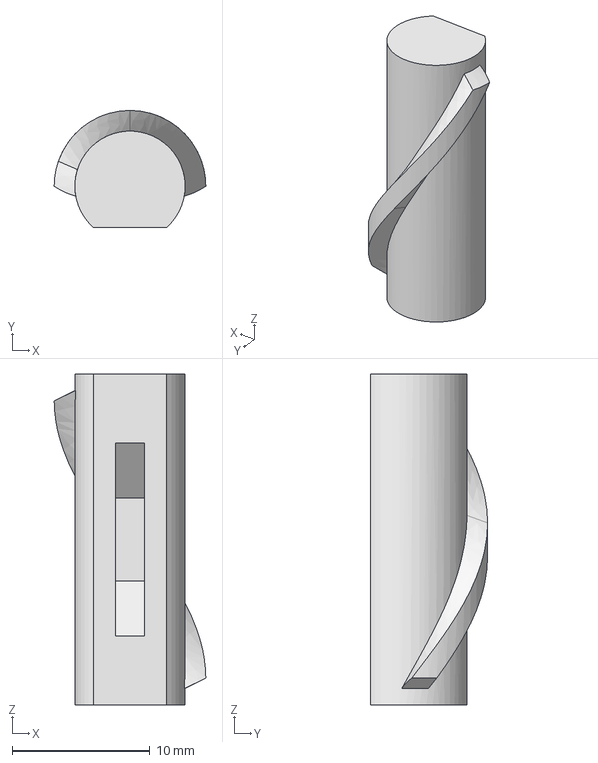
[picture p120: CAD file, 2025-03-15]
RealRails/SwitchLeverUnit_Roller.stp
11.0 x 8.50 x 24.0 mm
