kumarobo/PlaRails/RealRails/SwitchLeverUnit_Lever.stp

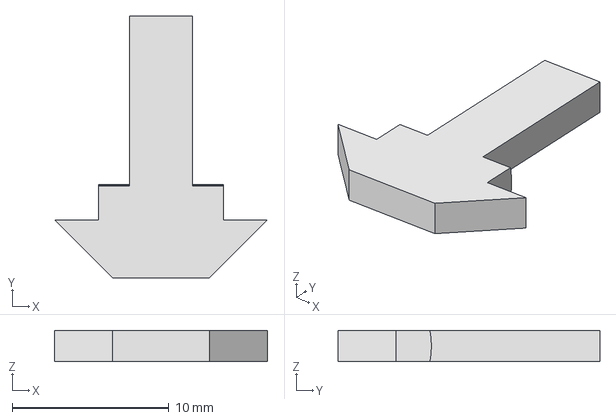
[picture p121: CAD file, 2025-03-15]
RealRails/SwitchLeverUnit_Lever.stp
13.6 x 16.7 x 2.00 mm
