kumarobo/PlaRails/RealRails/SwitchLeverUnit_UpperCase.stp

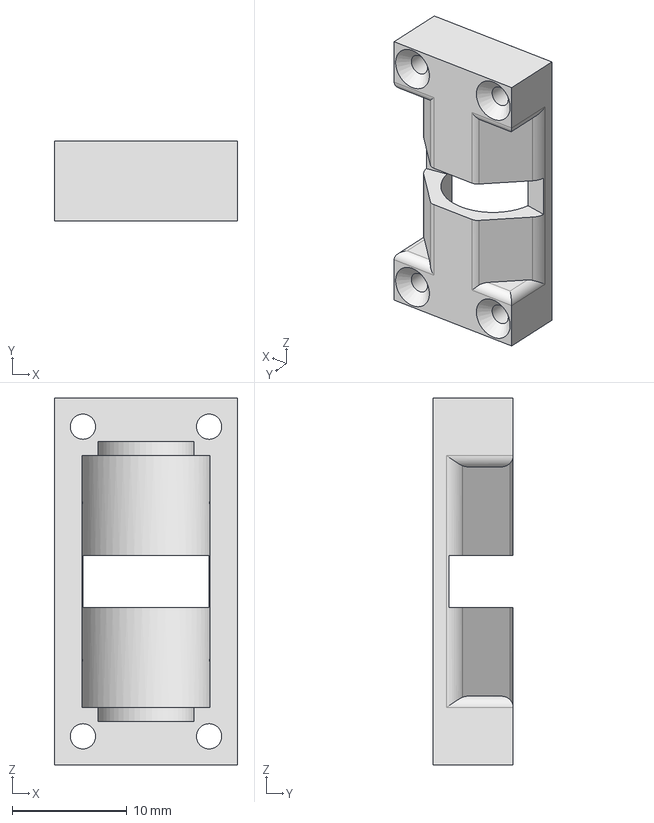
[picture p122: CAD file, 2025-03-15]
RealRails/SwitchLeverUnit_UpperCase.stp
16.0 x 7.00 x 32.0 mm
