kumarobo/PlaRails/RealRails/SwitchLeverUnit_LowerCase.stp

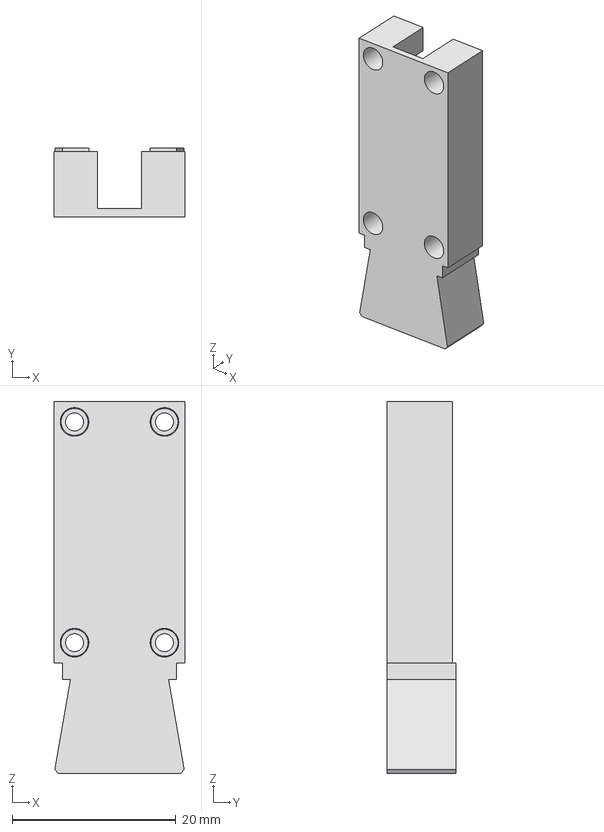
[picture p123: CAD file, 2025-03-15]
RealRails/SwitchLeverUnit_LowerCase.stp
16.0 x 8.40 x 45.5 mm
