kumarobo/PlaRails/DoubleCross/DoubleCross_Bar_printasm.png

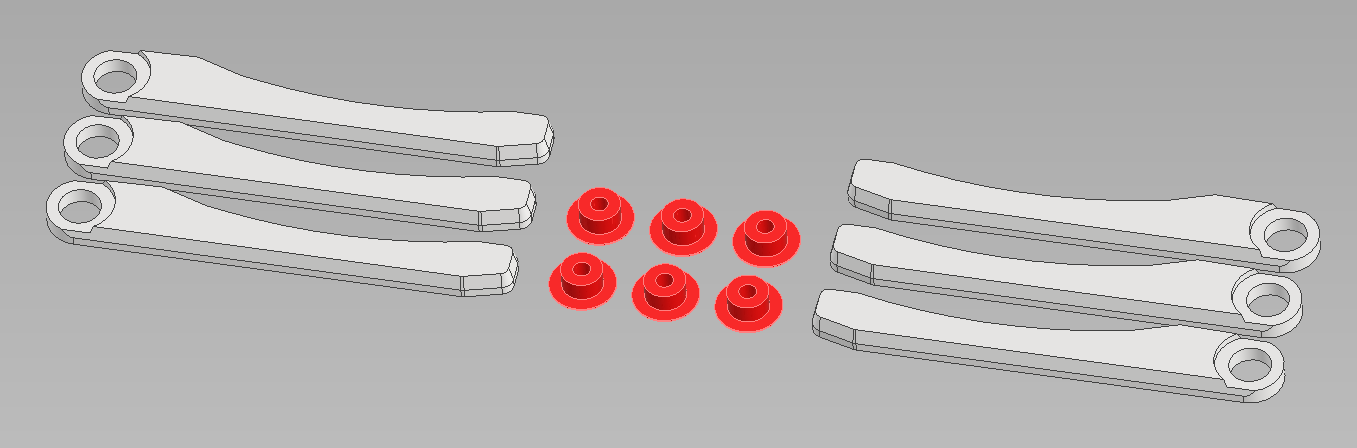
DoubleCross/DoubleCross_Bar_printasm.png
