kumarobo/PlaRails/PocketTrackPoint/pp_bar_printasm.png

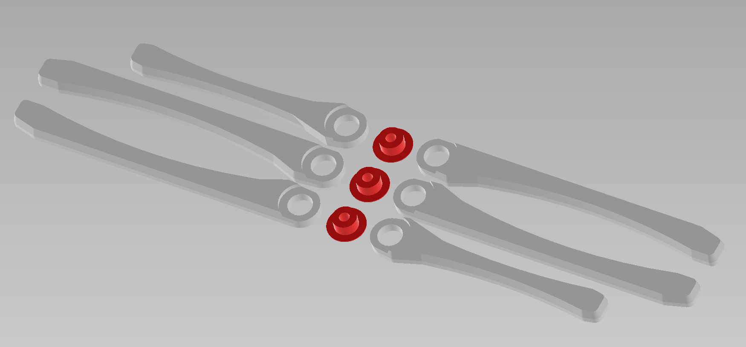
PocketTrackPoint/pp_bar_printasm.png
