kumarobo/PlaRails/TrussCC/TrussCC_printasm.png

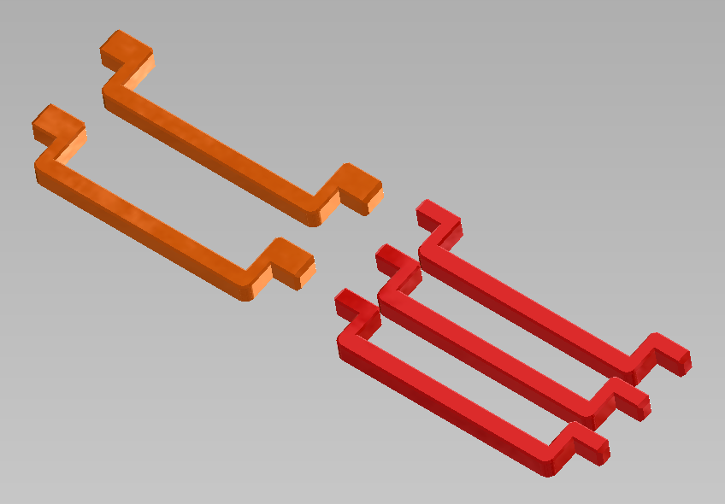
TrussCC/TrussCC_printasm.png
