kumarobo/PlaRails/DoubleCross/DoubleCross_Rturn_testasm.png

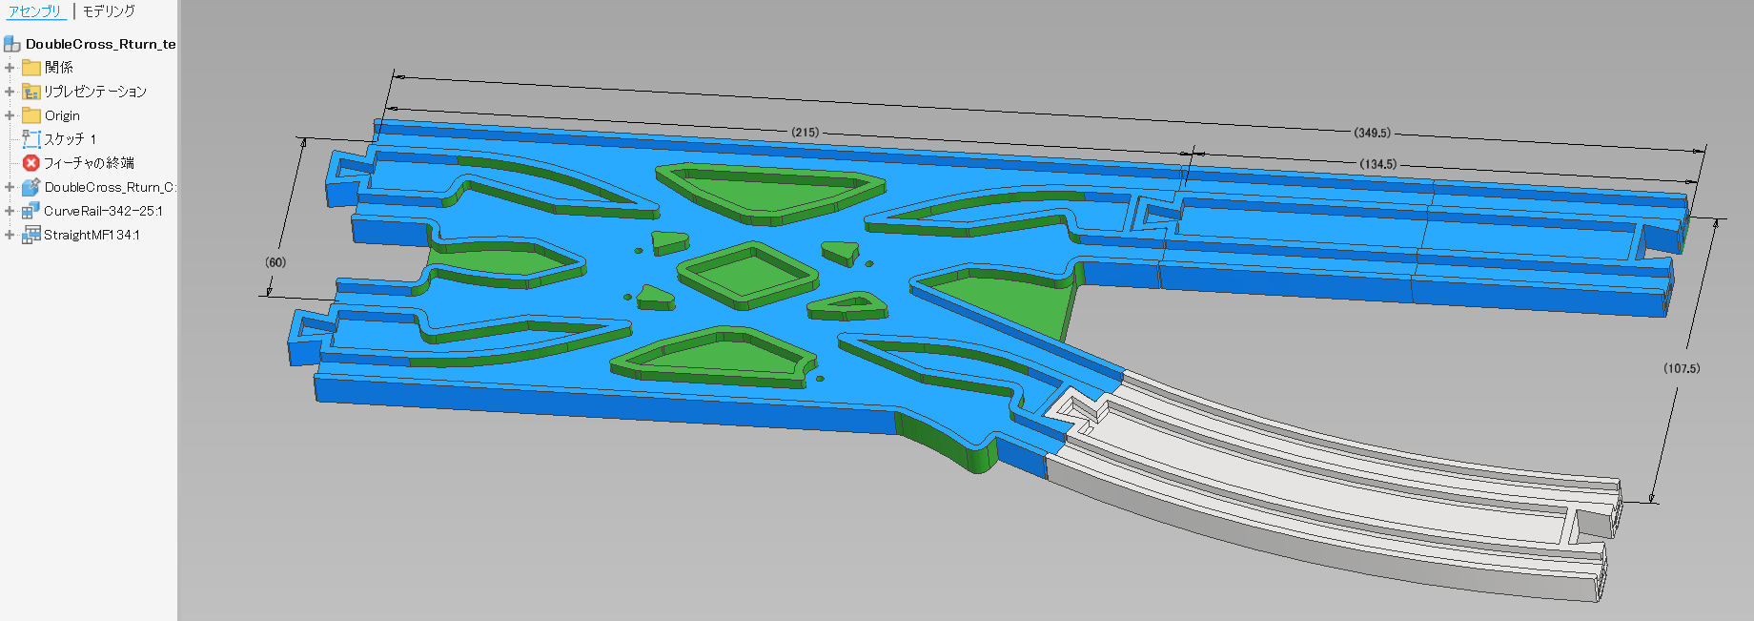
DoubleCross/DoubleCross_Rturn_testasm.png
