kumarobo/PlaRails/DoubleCross/DoubleCrossTestAsm.png

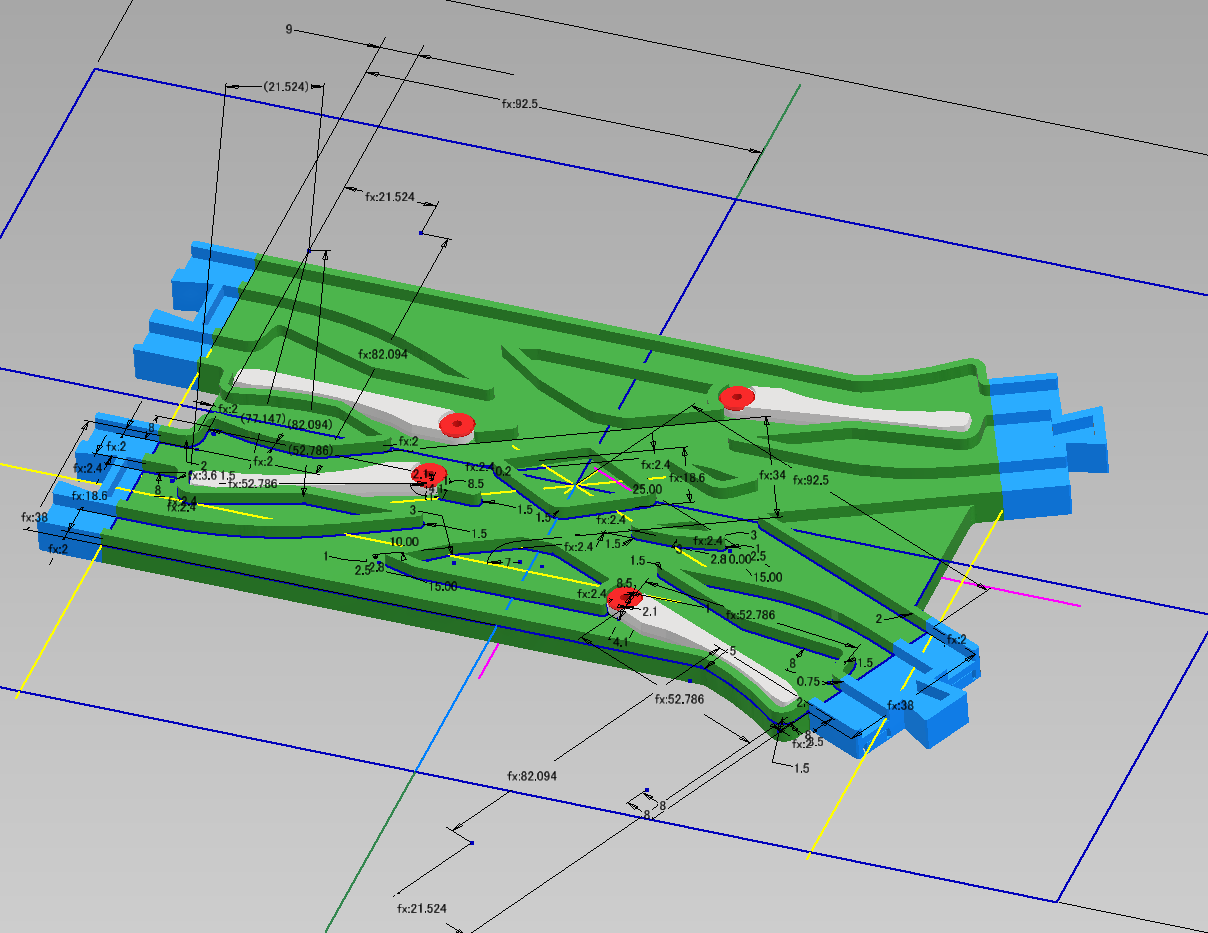
DoubleCross/DoubleCrossTestAsm.png
