kumarobo/PlaRails/TrussCC/TrussCC_testasm.png

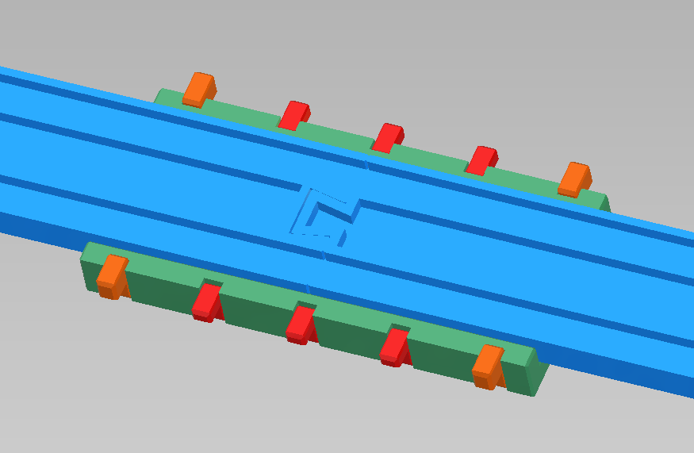
TrussCC/TrussCC_testasm.png
