kumarobo/PlaRails/VPUSlope/Slope_testasm2.png

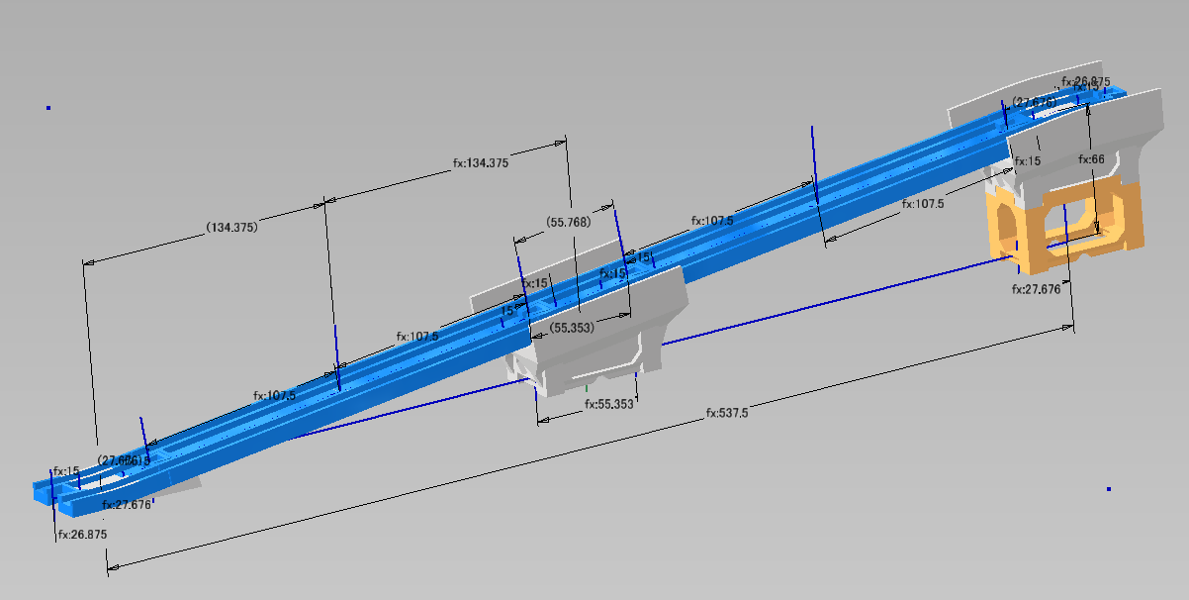
VPUSlope/Slope_testasm2.png
