kumarobo/PlaRails/VPUSlope/Slope_testasm.png

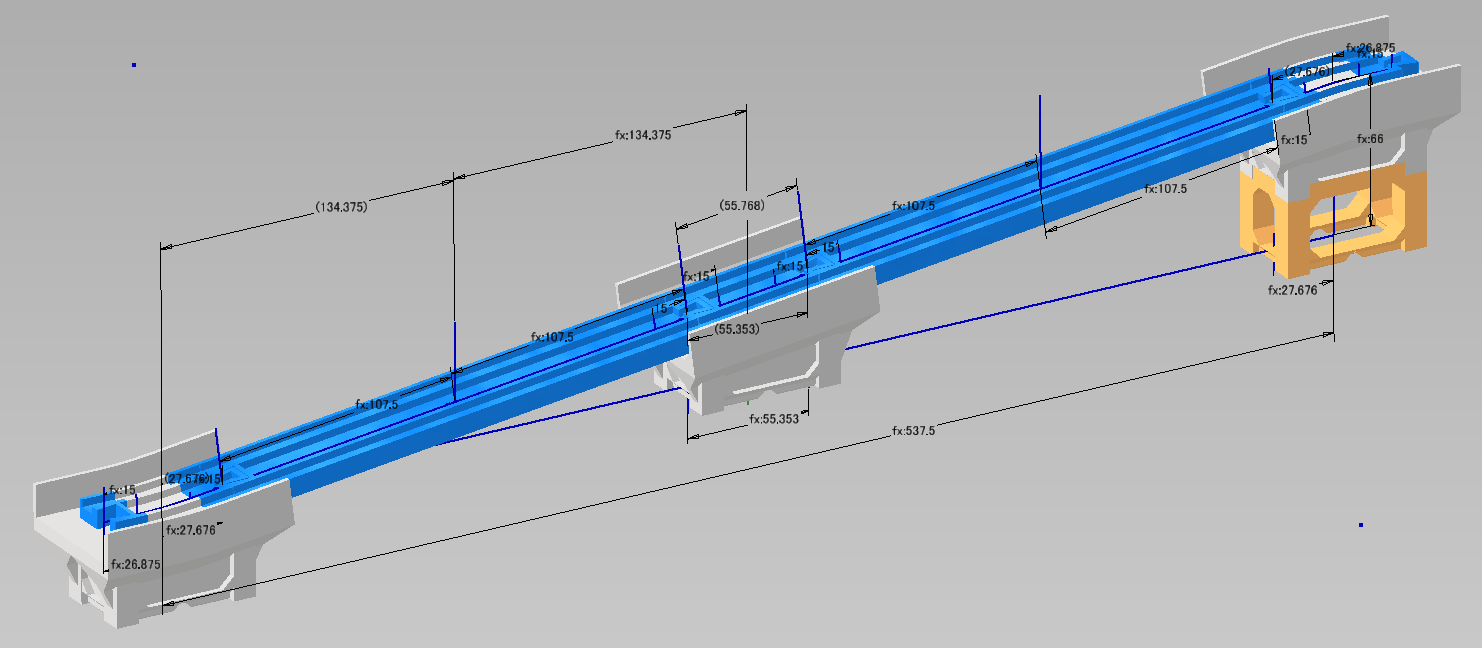
VPUSlope/Slope_testasm.png
